antonio1000homens/led/hardware/enclosure/parts/01_panel_hinge_template_PRINT_1.scad

hinge_part = "panel_template";
include <../direct_mount_enclosure.scad>;
