antonio1000homens/led/hardware/enclosure/parts/02_hinged_equipment_base_PRINT_1.scad

hinge_part = "equipment_base";
include <../direct_mount_enclosure.scad>;
