antonio1000homens/led/hardware/enclosure/parts/03_universal_equipment_backplane_PRINT_1.scad

hinge_part = "universal_backplane";
include <../direct_mount_enclosure.scad>;
