antonio1000homens/led/hardware/enclosure/parts/04_left_equipment_side_PRINT_1.scad

hinge_part = "side_left";
include <../direct_mount_enclosure.scad>;
