antonio1000homens/led/hardware/enclosure/parts/05_right_equipment_side_PRINT_1.scad

hinge_part = "side_right";
include <../direct_mount_enclosure.scad>;
