antonio1000homens/led/hardware/enclosure/parts/08_matrixportal_s3_dock_PRINT_1.scad

include <../matrixportal/matrixportal_s3_mount.scad>;

// Fixed side-carried dock. The two keyed tabs snap into the MatrixPortal CAD
// left / front-view-right side. The rear face is solid and runs clear of the
// backplane boss tips so the complete side/dock/controller can withdraw
// together. The carrier still slides in separately on its dovetails.
matrixportal_s3_dock_print();
