antonio1000homens/led/hardware/enclosure/parts/10_matrixportal_s3_carrier_PRINT_1.scad

include <../matrixportal/matrixportal_s3_mount.scad>;

// Removable raised carrier. The PCB remains attached to this part and the
// complete assembly slides into the fixed dock from the left service opening.
matrixportal_s3_carrier_print();
