antonio1000homens/led/hardware/enclosure/parts/10_panel_pair_joiner_PRINT_3.scad

include <../panel_pair_joiner.scad>;
panel_pair_joiners_print(3);
