antonio1000homens/led/hardware/enclosure/parts/11_matrixportal_s3_keeper_PRINT_1.scad

include <../matrixportal/matrixportal_s3_mount.scad>;

// Print two copies. Each bar locks one column of the MatrixPortal's two
// mounting holes onto the carrier's fixed printed locating pins.
matrixportal_s3_keeper_print();
