antonio1000homens/led/hardware/enclosure/powersupply/02_service_tray_snap_dock_PRINT_1.scad

// Printable fixed dock for issue #177 PSU service tray.
include <service_tray_snap_latch_common.scad>;
snap_dock();
