antonio1000homens/led/hardware/enclosure/powersupply/03_service_tray_snap_tray_PRINT_1.scad

// Printable removable tray with integral pull-release flexure for issue #177.
include <service_tray_snap_latch_common.scad>;

// Stand the plate on its long lower edge. This puts the flexure anchor at the
// first layers so the 30 mm cantilever builds upward. The H2D process profile
// must enable support for the flexure. Z=0 is the tray's Y=+39.5 edge.
translate([0,0,tray_h/2])
    rotate([-90,0,0])
        snap_tray_with_detent();
