antonio1000homens/led/hardware/enclosure/schematics/00_complete_enclosure_CLOSED_ASSEMBLY.scad

// Complete four-module LED enclosure in the fully closed position.
// Assembly/reference view only; not a printable part.

include <../direct_mount_enclosure.scad>;

complete_direct_mount_assembly(0);
