antonio1000homens/led/hardware/enclosure/schematics/00_hinged_enclosure_ASSEMBLY.scad

hinge_part = "assembly";
include <../direct_mount_enclosure.scad>;
