antonio1000homens/led/hardware/enclosure/schematics/00_hinged_enclosure_CLOSED_ASSEMBLY.scad

include <../direct_mount_enclosure.scad>;
direct_mount_assembly(0);
