antonio1000homens/led/hardware/enclosure/schematics/matrixportal_s3_REFERENCE.scad

include <../matrixportal/matrixportal_s3_mount.scad>;

// Official Eagle-derived mechanical reference. This is not a printable part.
matrixportal_s3_reference(true);
