antonio1000homens/led/hardware/enclosure/direct-mount/parts/01_backplane_module_PRINT_3.scad

part = "backplane";
include <../direct_mount_enclosure.scad>;
