antonio1000homens/led/hardware/enclosure/direct-mount/parts/02_module_joiner_PRINT_4.scad

part = "joiner";
include <../direct_mount_enclosure.scad>;
