antonio1000homens/led/hardware/enclosure/direct-mount/parts/03_rod_end_plug_PRINT_4.scad

part = "rod_plug";
include <../direct_mount_enclosure.scad>;
