antonio1000homens/led/hardware/enclosure/direct-mount/parts/04_matrixportal_mount_PRINT_1.scad

part = "matrixportal_mount";
include <../direct_mount_enclosure.scad>;
