antonio1000homens/led/hardware/enclosure/direct-mount/parts/06_cable_clip_PRINT_8.scad

part = "cable_clip";
include <../direct_mount_enclosure.scad>;
