antonio1000homens/led/hardware/enclosure/direct-mount/parts/07_mounting_slot_coupon_PRINT_1.scad

part = "slot_coupon";
include <../direct_mount_enclosure.scad>;
