antonio1000homens/led/hardware/enclosure/direct-mount/parts/08_mount_pattern_template_PRINT_1.scad

part = "mount_pattern_template";
include <../direct_mount_enclosure.scad>;
