antonio1000homens/led/hardware/enclosure/direct-mount/docs/MECHANICAL_VALIDATION.md

# Hinged enclosure mechanical validation

The modular hinged design is the only supported direct-mount enclosure.

The canonical hinge motion follows PR #119: the equipment-side enclosure/base
remains stationary and the LED panel/template is the moving leaf.

## Automated gates

Run:

```bash
python hardware/enclosure/direct-mount/scripts/validate_enclosure.py
```

The validator regenerates all five canonical OpenSCAD parts and verifies:

- non-empty positive-volume meshes;
- watertight/single-shell geometry after mesh processing;
- bounded printable extents;
- a 2 mm voxel floating-layer/island proxy;
- no volumetric interference between the stationary base and removable backplane;
- positive backplane seating in the recessed rear base groove;
- top-down insertion clearance and 0.4 mm nominal groove clearance;
- dual **30 mm × 5 mm** structural side guides with 0.4 mm running clearance;
- the lower 30 mm stepped/narrowed backplane section and full-width shoulder above it;
- hidden guide-tower junctions kept within the bed-connected lower band;
- blind inside accessory bosses with a solid external rear skin;
- the 2 mm seat depth and rear-edge groove location;
- the 40 mm lower cavity, 60 mm taper start and 10 mm top depth;
- upper-only ventilation and the supported top closure;
- side-piece fit and hinge-rod clearance;
- an unobstructed lower equipment volume ahead of the rear groove;
- the stationary enclosure and 6 mm rail against the moving panel/template at
  **0, 15, 30, 45, 60, 75 and 90°**;
- neighboring module cores at the 256 mm pitch, with side retainers only at
  the outside edges;
- successful open and closed assembly-preview rendering.

The hinge regression contract includes:

- **14 mm** barrel OD;
- **7.2 mm** printed bore for the 6 mm rail;
- hinge axis at **y=27 mm, z=16 mm**;
- **7 mm** closed template-to-barrel clearance;
- local roots on the moving template only;
- rearward support webs that terminate at the reinforced hinge shelf;
- 3 mm local pads at the stationary hinge roots;
- **2 mm** stationary lower guard with **0.8 mm** barrel clearance.

The previous full-width captive tongue/channel is retired. The backplane enters
a 2 mm-deep **recessed groove at the rear of the base**. Its lower section is
vertical at the 40 mm equipment depth up to 60 mm; the upper enclosure then
tapers to 10 mm, carries ventilation slots, and grows a supported top closure
toward the moving template. The validator checks the rear-groove contract,
several positions along the vertical insertion path, the lower usable cavity,
and the complete hinge sweep.

The final automated manufacturing gate is Windsor Slicer/Bambu Studio using the
models in `.windsor-slicer.yaml`.

## Physical gates

Automated geometry cannot prove real FDM tolerances. Before printing four full
sets:

1. print one moving panel/template leaf and verify the six physical panel bosses;
2. print one stationary equipment base and verify the real 6 mm rail;
3. rotate the panel/template through the full **0–90°** arc while the equipment base remains fixed;
4. confirm the moving panel never contacts the stationary barrel support webs or lower guard;
5. print one universal backplane and confirm the narrowed lower 30 mm slides between both 5 mm guides, seats 2 mm into the rear groove, and removes upward;
6. confirm the guide towers retain the backplane laterally and the full-width shoulder clears their tops;
7. confirm the vertical lower wall, ventilated taper and top closure print without distortion;
8. verify the hidden guide-tower junctions and both outer side pieces engage while all exterior faces remain solid;
9. mate two equipment cores side-by-side at the 256 mm pitch and check the hidden pin/socket alignment;
10. test representative M3 hardware on the inward-facing lower boss grid and verify the external rear skin is unbroken;
11. verify connected HUB75/power cabling remains free through the opening arc.

Record tolerance changes in `direct_mount_enclosure.scad`; never patch an STL directly.
