antonio1000homens/led/hardware/matrixportal/firmware/display.py

"""Display backends: MatrixPortal S3 hardware and Wokwi visual fixture."""

import time

import board

from matrix_config import (
    MATRIX_ANIMATION_PROFILE,
    MATRIX_ANIMATION_PROFILES,
    MATRIX_BIT_DEPTH,
    MATRIX_EXPERIMENT_PRESET,
    CALLING_SCROLL_SPEED_OVERRIDE,
    MATRIX_PRESENTATION_MODE,
    MATRIX_RAIL_ROWS_SCROLL,
    MATRIX_REFRESH_FPS,
    MATRIX_STATS_INTERVAL_SECONDS,
    TODOIST_MARQUEE_PAUSE_SECONDS,
    TODOIST_MARQUEE_SPEED,
)

from brightness import BrightnessState, pixel_is_blocked

from formatting import (
    AGENDA_SLIDE_SECONDS,
    AGENDA_TITLE_X,
    AGENDA_VISIBLE_ROWS,
    QUEUE_VISIBLE_ROWS,
    agenda_scroll_state,
    agenda_marquee_x,
    agenda_title_marquee_x,
    calendar_due_text,
    todoist_due_label,
    calendar_row_parts,
    calendar_row_text,
    CALLING_LABEL,
    RAIL_MARQUEE_DELAY_SECONDS,
    CALLING_MARQUEE_PAUSE_SECONDS,
    calling_marquee_x,
    calling_color_segments,
    calling_text,
    rail_calling_timing,
    departure_scroll_state,
    DEPARTURE_SLIDE_SECONDS,
    DEPARTURE_RESET_GAP_SECONDS,
    DEPARTURE_RESET_SLIDE_SECONDS,
    RAIL_ROW_Y,
    RAIL_CALLING_SECONDS,
    RAIL_SUMMARY_SECONDS,
    rail_marquee_elapsed,
    rail_phase,
    rail_rows,
    ordinal_label,
    format_row,
    queue_scroll_state,
    row_slide_phase,
    service_status_text,
)


DISPLAY_WIDTH = 256
REMINDER_CLOCK_SIZE = 29
REMINDER_TEXT_X = 37
REMINDER_TEXT_SCALE = 3
REMINDER_SCROLL_SPEED = 64.0
REMINDER_SCROLL_GAP = 24


def reminder_scroll_x(screen, phase):
    """Continuously move the clock/text train from right to left and wrap it."""
    label = str(screen.get("label") or "")
    width = REMINDER_TEXT_X + len(label) * WEATHER_FONT_WIDTH * REMINDER_TEXT_SCALE
    travel = DISPLAY_WIDTH + width + REMINDER_SCROLL_GAP
    try:
        elapsed = max(0.0, float(phase or 0))
    except (TypeError, ValueError):
        elapsed = 0.0
    distance = int(elapsed * REMINDER_SCROLL_SPEED) % max(1, travel)
    return DISPLAY_WIDTH - distance


def reminder_clock_pixel(x, y):
    dx, dy = x - 14, y - 14
    return (156 <= dx * dx + dy * dy <= 205
            or (13 <= x <= 15 and 5 <= y <= 15)
            or (14 <= x <= 22 and 13 <= y <= 15))


STEAM_TRAIN_WIDTH = 52
STEAM_TRAIN_HEIGHT = 26
STEAM_TRAIN_VERTICAL_OFFSET = 1
STEAM_TRAIN_TEXT_GAP = 8
CLOCK_X = 226
HEADER_SLOT_X = 224
STALE_X = 190
QUEUE_FIRST_Y = 11
QUEUE_ROW_HEIGHT = 8
# The font label coordinate is a baseline. Start the three agenda rows lower
# so the final row uses the bottom of the 32px panel instead of leaving a
# visible unused band below it.
AGENDA_FIRST_Y = 11
AGENDA_ROW_HEIGHT = 8
WEATHER_ICON_WIDTH = 7
WEEKLY_WEATHER_ICON_SCALE = 2
TODAY_WEATHER_ICON_SCALE = 2
SUN_WEATHER_ICON_SCALE = 3
SUN_WEATHER_MOON_ICON_SCALE = 2
SUN_WEATHER_TIME_SCALE = 2
SUN_WEATHER_SUN_COLOR = 0xFFFF00
SUN_WEATHER_MOON_COLOR = 0x0000FF
SUN_WEATHER_ICON_Y = 5
SUN_WEATHER_ANIMATION_SECONDS = 4.0
SUN_WEATHER_COLOR_SECONDS = 4.0
SUN_WEATHER_TOTAL_ANIMATION_SECONDS = SUN_WEATHER_ANIMATION_SECONDS * 2
SUN_WEATHER_RISE_START_Y = 32
SUN_WEATHER_SET_START_Y = -(WEATHER_ICON_WIDTH * SUN_WEATHER_MOON_ICON_SCALE)
# MatrixDisplay labels use font baselines, while the fixture renderer uses
# top-left pixel coordinates. Keep fullscreen weather headers clear of the
# panel edge and align the forecast rows below them.
WEATHER_HEADING_BASELINE_Y = 9
WEATHER_HEADING_PIXEL_Y = 2
WEEKLY_WEATHER_ICON_Y = 10
WEEKLY_WEATHER_TEMPERATURE_Y = 25
TODAY_WEATHER_ICON_Y = 11
TODAY_WEATHER_TEMPERATURE_Y = 27
WEATHER_FULLSCREEN_KINDS = ("weather_weekly", "weather_today", "weather_sun")
NOVELTY_HEADING_Y = 5
NOVELTY_FIRST_LINE_Y = 14


def _novelty_page(screen, phase):
    """Wrap novelty text, advancing longer facts across pages during their slot."""
    message = str(screen.get("joke") if screen.get("kind") == "dad_joke" else screen.get("fact") or "")
    lines, current = [], ""
    for word in message.split():
        # Split unusually long uninterrupted words rather than silently clipping.
        while len(word) > 42:
            if current:
                lines.append(current)
                current = ""
            lines.append(word[:42])
            word = word[42:]
        if not word:
            continue
        candidate = (current + " " + word).strip()
        if len(candidate) > 42 and current:
            lines.append(current)
            current = word
        else:
            current = candidate
    if current:
        lines.append(current)
    if not lines:
        return []
    pages = (len(lines) + 2) // 3
    duration = max(1.0, float(screen.get("duration_seconds") or 15))
    page = min(pages - 1, int(max(0.0, float(phase)) * pages / duration))
    return lines[page * 3:page * 3 + 3]

WEEKLY_WEATHER_TEXT_SCALE = 1
WEEKLY_WEATHER_GLYPH_WIDTH = 3
WEEKLY_WEATHER_GLYPHS = {
    "0": (7, 5, 5, 5, 7), "1": (2, 6, 2, 2, 7),
    "2": (7, 1, 7, 4, 7), "3": (7, 1, 7, 1, 7),
    "4": (5, 5, 7, 1, 1), "5": (7, 4, 7, 1, 7),
    "6": (7, 4, 7, 5, 7), "7": (7, 1, 2, 2, 2),
    "8": (7, 5, 7, 5, 7), "9": (7, 5, 7, 1, 7),
    "S": (7, 4, 7, 1, 7), "U": (5, 5, 5, 5, 7),
    "N": (5, 7, 7, 7, 5), "R": (6, 5, 6, 5, 5),
    "I": (7, 2, 2, 2, 7), "E": (7, 4, 6, 4, 7),
    "T": (7, 2, 2, 2, 2), ":": (0, 4, 0, 4, 0),
    "C": (3, 4, 4, 4, 3), "-": (0, 0, 7, 0, 0),
}
WEATHER_FONT_WIDTH = 5
WEATHER_GAP = 1
HEADER_GAP = 4
HEADER_HOLD_SECONDS = 7.0
HEADER_SLOT_WIDTH = DISPLAY_WIDTH - HEADER_SLOT_X
CALLING_SCROLL_SPEED = 20.0
CALLING_SCROLL_GAP = 28
MIN_CALLING_SCROLL_SPEED = 10.0
MAX_CALLING_SCROLL_SPEED = 80.0
MIN_CALLING_SCROLL_GAP = 8
MAX_CALLING_SCROLL_GAP = 80
BIN_LORRY_SECONDS = 4.0
BIN_LORRY_SPEED = 64.0
BIN_LORRY_WIDTH = 52
BIN_LORRY_HEIGHT = 20
BIN_ICON_WIDTH = 9
BIN_ICON_HEIGHT = 12
BIN_ICON_Y = 10
BIN_TEXT_X = 40
BIN_TEXT_RIGHT = 220
BIN_COLORS = {
    "blue": 0x2255FF,
    "green": 0x22AA44,
    "black": 0x777777,
}
RAIL_ORDINAL_X = 0
RAIL_TIME_X = 24
RAIL_DESTINATION_X = 60
RAIL_PLATFORM_X = 152
RAIL_PLATFORM_WIDTH = 3 * WEATHER_FONT_WIDTH

WEATHER_ICONS = {
    # A compact round sun: the filled centre reads as a disc while the
    # separated cardinal and diagonal pixels remain visible at LED scale.
    "clear_day": (".......", "..###..", ".#####.", ".#####.", ".#####.", "..###..", "......."),
    "clear_night": ("...###.", "..###..", ".###...", ".###...", ".####..", "..####.", "...###."),
    "partly_cloudy_day": (".#.#...", "..#....", ".###...", "...##..", "..#####", ".######", "......."),
    "partly_cloudy_night": ("..##...", ".##....", ".###...", "...##..", "..#####", ".######", "......."),
    "cloudy": (".......", "...##..", "..####.", ".######", "#######", ".......", "......."),
    "fog": (".......", ".#####.", ".......", "#######", ".......", ".#####.", "......."),
    "rain": ("...##..", "..####.", ".######", "#######", "..#.#..", ".#.#...", "#.#...."),
    "snow": ("...##..", "..####.", ".######", "#######", ".#.#.#.", "..#.#..", ".#.#.#."),
    "storm": ("...##..", "..####.", ".######", "#######", "...##..", "..##...", "...#..."),
    "unknown": (".#####.", "##...##", "....##.", "...##..", "..##...", ".......", "..##..."),
}

WEATHER_COLORS = {
    "clear_day": 0xFFAA00,
    "clear_night": 0xAACCFF,
    "partly_cloudy_day": 0xFFCC55,
    "partly_cloudy_night": 0xAACCFF,
    "cloudy": 0xBBBBBB,
    "fog": 0x888888,
    "rain": 0x55AAFF,
    "snow": 0xFFFFFF,
    "storm": 0xFFCC00,
    "unknown": 0x888888,
}


def _clip(value, width):
    return str(value or "")[:max(0, int(width or 0))]


def _queue_parts(ride):
    state = "{}m".format(ride.get("wait_minutes", 0)) if ride.get("open") else "CLOSED"
    return str(ride.get("name") or "Unknown"), state


def _queue_row(ride):
    name, state = _queue_parts(ride)
    name = _clip(name, 24)
    name = name + (" " * max(0, 24 - len(name)))
    state = (" " * max(0, 8 - len(state))) + state
    return (name + state)[-32:]


def _weather_text(weather):
    if not isinstance(weather, dict):
        return None
    value = weather.get("temperature_c")
    if value is None:
        return "--C"
    try:
        return "{}C".format(int(round(float(value))))
    except (TypeError, ValueError):
        return "--C"


def _weather_icon(weather):
    if not isinstance(weather, dict):
        return None, WEATHER_ICONS["unknown"]
    name = str(weather.get("icon") or "unknown")
    return name, WEATHER_ICONS.get(name, WEATHER_ICONS["unknown"])


def _weather_rgb(icon_name, stale=False):
    color = WEATHER_COLORS.get(icon_name, WEATHER_COLORS["unknown"])
    return 0x777777 if stale else color


def _rail_weather_key(weather):
    """Return only weather fields that affect visible rail pixels."""
    if not isinstance(weather, dict):
        return None
    icon_name, _ = _weather_icon(weather)
    return (_weather_text(weather), icon_name, bool(weather.get("stale")))


def _next_periodic_boundary(elapsed, boundaries, cycle):
    """Seconds to the next state edge in a repeating animation cycle."""
    cycle = max(0.001, float(cycle))
    within = max(0.0, float(elapsed or 0)) % cycle
    candidates = []
    for boundary in boundaries:
        edge = float(boundary) % cycle
        delta = edge - within
        if delta <= 1e-6:
            delta += cycle
        candidates.append(delta)
    return min(candidates) if candidates else cycle


def _header_content_right(screen):
    return max(0, (STALE_X if screen.get("stale") else HEADER_SLOT_X) - HEADER_GAP)


def _right_aligned_x(text, right_edge):
    return max(0, int(right_edge) - len(str(text or "")) * WEATHER_FONT_WIDTH)


def _left_text(text, right_edge):
    return _clip(text, max(0, int(right_edge) // WEATHER_FONT_WIDTH))


def _fit_text_pixels(text, width):
    return _clip(text, max(0, int(width) // WEATHER_FONT_WIDTH))


def _weather_column_bounds(index, display_width=DISPLAY_WIDTH):
    """Return integer seven-column bounds without accumulating rounding error."""
    left = (int(index) * int(display_width)) // 7
    right = ((int(index) + 1) * int(display_width)) // 7
    return left, right


def _weekly_temperature_text(value):
    try:
        rounded = int(round(float(value)))
    except (TypeError, ValueError):
        return "--C"
    return "{}C".format(rounded)


def _weekly_weather_layout(days, display_width=DISPLAY_WIDTH):
    """Build renderer-neutral positions for up to seven forecast days."""
    if not isinstance(days, (list, tuple)):
        return []
    layout = []
    for index, raw_day in enumerate(days[:7]):
        day = raw_day if isinstance(raw_day, dict) else {}
        left, right = _weather_column_bounds(index, display_width)
        width = right - left
        weekday = _fit_text_pixels(str(day.get("weekday") or "").upper()[:3], width)
        maximum = _weekly_temperature_text(day.get("temperature_max_c"))
        icon_width = WEATHER_ICON_WIDTH * WEEKLY_WEATHER_ICON_SCALE
        maximum_width = len(maximum) * (WEEKLY_WEATHER_GLYPH_WIDTH + 1) * WEEKLY_WEATHER_TEXT_SCALE
        icon_name, rows = _weather_icon(day)

        def centered_x(text, pixel_width):
            return left + max(0, (width - pixel_width) // 2)

        layout.append({
            "index": index,
            "left": left,
            "right": right,
            "weekday": weekday,
            "weekday_x": centered_x(weekday, len(weekday) * WEATHER_FONT_WIDTH),
            "icon_name": icon_name,
            "icon_rows": rows,
            "icon_x": centered_x("", icon_width),
            "max_text": maximum,
            "max_x": left + max(0, (width - maximum_width) // 2),
            "icon_width": icon_width,
        })
    return layout


def _sun_weather_progress(phase):
    """Return the bounded entry-animation progress for the solar icons."""
    try:
        elapsed = max(0.0, float(phase or 0))
    except (TypeError, ValueError):
        elapsed = 0.0
    return min(1.0, elapsed / SUN_WEATHER_ANIMATION_SECONDS)


def _sun_weather_animation_active(phase):
    try:
        elapsed = max(0.0, float(phase or 0))
    except (TypeError, ValueError):
        elapsed = 0.0
    return elapsed < SUN_WEATHER_TOTAL_ANIMATION_SECONDS


def _sun_weather_local_phase(icon_name, phase):
    """Return the phase for one solar event in the sequential animation."""
    try:
        elapsed = max(0.0, float(phase or 0))
    except (TypeError, ValueError):
        elapsed = 0.0
    if icon_name == "clear_night":
        elapsed -= SUN_WEATHER_ANIMATION_SECONDS
    return min(SUN_WEATHER_ANIMATION_SECONDS, max(0.0, elapsed))


def _bin_collection_motion_state(screen, phase):
    """Return whether the bin lorry or collection label is moving."""
    try:
        elapsed = max(0.0, float(phase or 0))
    except (TypeError, ValueError):
        elapsed = 0.0
    if elapsed < BIN_LORRY_SECONDS:
        return True, max(0.05, BIN_LORRY_SECONDS - elapsed)
    labels = " / ".join(str(item.get("label") or "") for item in screen.get("collections") or [])
    label_width = len(labels) * 6
    if label_width <= BIN_TEXT_RIGHT - BIN_TEXT_X:
        return False, None
    try:
        speed = max(0.1, float(screen.get("slide_speed") or 20))
        elapsed = max(0.0, float(phase or 0))
    except (TypeError, ValueError):
        speed, elapsed = 20.0, 0.0
    cycle_distance = label_width + 24
    distance = (max(0.0, elapsed - BIN_LORRY_SECONDS) * speed) % cycle_distance
    if distance < label_width:
        return True, None
    return False, max(0.05, (cycle_distance - distance) / speed)


def _bin_collection_types(screen):
    """Map Home Assistant collection IDs to the bins shown on the board."""
    items = screen.get("collections") or []
    ids = " ".join(str(item.get("id") or "").lower() for item in items)
    labels = " ".join(str(item.get("label") or "").lower() for item in items)
    if "paper" in ids or "paper" in labels:
        return ("blue", "green", "black")
    if any(token in ids or token in labels for token in ("plastic", "plastics", "recycle-mixed")):
        return ("green",)
    return ("green",)


def _date_ordinal(value):
    """Convert a strict YYYY-MM-DD date to a Gregorian day number."""
    if not isinstance(value, str) or len(value) != 10 or value[4] != "-" or value[7] != "-":
        return None
    if not (value[:4].isdigit() and value[5:7].isdigit() and value[8:10].isdigit()):
        return None
    try:
        year, month, day = int(value[:4]), int(value[5:7]), int(value[8:10])
    except ValueError:
        return None
    if year < 1 or not 1 <= month <= 12:
        return None
    leap = year % 4 == 0 and (year % 100 != 0 or year % 400 == 0)
    month_lengths = (31, 29 if leap else 28, 31, 30, 31, 30, 31, 31, 30, 31, 30, 31)
    if not 1 <= day <= month_lengths[month - 1]:
        return None
    previous_year = year - 1
    days = previous_year * 365 + previous_year // 4 - previous_year // 100 + previous_year // 400
    days += sum(month_lengths[:month - 1]) + day - 1
    return days


def _bin_collection_due_label(collection_date, today):
    due_day = _date_ordinal(collection_date)
    today_day = _date_ordinal(today)
    if due_day is None or today_day is None:
        return "DUE DATE UNKNOWN"
    days_until = due_day - today_day
    if days_until < 0:
        return "OVERDUE"
    if days_until == 0:
        return "DUE TODAY"
    if days_until == 1:
        return "DUE IN 1 DAY"
    return "DUE IN {} DAYS".format(days_until)


def _bin_lorry_x(phase):
    """Slide a compact refuse lorry across the board from right to left."""
    try:
        elapsed = max(0.0, float(phase or 0))
    except (TypeError, ValueError):
        elapsed = 0.0
    return int(round(DISPLAY_WIDTH - elapsed * BIN_LORRY_SPEED))


def _format_sun_time(value):
    """Keep the time separator visible and normalize compact HHMM values."""
    text = str(value or "--:--")
    if len(text) == 4 and text.isdigit():
        return text[:2] + ":" + text[2:]
    return text


def _sun_weather_icon_y(icon_name, phase):
    """Slide sunrise upward and sunset downward to their shared resting row."""
    progress = _sun_weather_progress(_sun_weather_local_phase(icon_name, phase))
    # Smoothstep eases the icons into their final row instead of moving at a
    # constant speed and stopping abruptly. The clamped endpoint remains on
    # the panel for the rest of this screen's duration.
    progress = progress * progress * (3.0 - 2.0 * progress)
    if icon_name == "clear_day":
        icon_scale = SUN_WEATHER_ICON_SCALE
        start_y = SUN_WEATHER_RISE_START_Y
    elif icon_name == "clear_night":
        icon_scale = SUN_WEATHER_MOON_ICON_SCALE
        start_y = SUN_WEATHER_SET_START_Y
    else:
        return SUN_WEATHER_ICON_Y
    icon_size = WEATHER_ICON_WIDTH * icon_scale
    tile_size = WEATHER_ICON_WIDTH * SUN_WEATHER_ICON_SCALE
    rest_y = SUN_WEATHER_ICON_Y + (tile_size - icon_size) // 2
    return int(round(start_y + (rest_y - start_y) * progress))


def _sun_weather_color_progress(phase):
    try:
        elapsed = max(0.0, float(phase or 0))
    except (TypeError, ValueError):
        elapsed = 0.0
    progress = min(1.0, elapsed / SUN_WEATHER_COLOR_SECONDS)
    return progress * progress * (3.0 - 2.0 * progress)


def _sun_weather_rise_label_color(index, phase, stale=False):
    if stale:
        return 0x777777
    progress = _sun_weather_color_progress(_sun_weather_local_phase("clear_day", phase))
    yellow_letters = min(7, int(progress * 8))
    return 0xFFFF00 if index < yellow_letters else 0x0000FF


def _sun_weather_set_label_color(index, phase, stale=False):
    progress = _sun_weather_color_progress(_sun_weather_local_phase("clear_night", phase))
    # Reveal one additional sunset letter at a time from yellow to blue.
    blue_letters = min(6, int(progress * 7))
    if index < blue_letters:
        return 0x777777 if stale else 0x0000FF
    return 0x777777 if stale else 0xFFAA00


def _sun_weather_rgb(icon_name, stale=False, phase=0):
    """Keep the sunrise sun yellow and the moon blue throughout the animation."""
    if stale:
        return 0x777777
    if icon_name == "clear_night":
        return SUN_WEATHER_MOON_COLOR
    return SUN_WEATHER_SUN_COLOR


def _today_weather_layout(blocks, display_width=DISPLAY_WIDTH):
    """Build six rolling four-hour Weather columns beginning with Now."""
    if not isinstance(blocks, (list, tuple)):
        return []
    layout = []
    for index, raw_block in enumerate(blocks[:6]):
        block = raw_block if isinstance(raw_block, dict) else {}
        left = (index * int(display_width)) // 6
        right = ((index + 1) * int(display_width)) // 6
        width = right - left
        label = str(block.get("label") or "")[:5]
        temperature = _weekly_temperature_text(block.get("temperature_c"))
        icon_name, rows = _weather_icon(block)
        icon_width = WEATHER_ICON_WIDTH * TODAY_WEATHER_ICON_SCALE
        temp_width = len(temperature) * (WEEKLY_WEATHER_GLYPH_WIDTH + 1)
        layout.append({
            "left": left,
            "right": right,
            "label": label,
            "label_x": left + max(0, (width - len(label) * WEATHER_FONT_WIDTH) // 2),
            "icon_name": icon_name,
            "icon_rows": rows,
            "icon_x": left + max(0, (width - icon_width) // 2),
            "icon_width": icon_width,
            "temp_text": temperature,
            "temp_x": left + max(0, (width - temp_width) // 2),
        })
    return layout


def _calling_segments(text, x, gap):
    """Return clipped station-label segments that cannot overwrite the prefix."""
    text = str(text or "")
    stations = text[len(CALLING_LABEL):] if text.startswith(CALLING_LABEL) else text
    station_width = len(stations) * WEATHER_FONT_WIDTH
    prefix_width = len(CALLING_LABEL) * WEATHER_FONT_WIDTH
    segments = []
    for candidate_x in (int(x), int(x) + station_width + int(gap)):
        if candidate_x >= DISPLAY_WIDTH or candidate_x + station_width <= prefix_width:
            continue
        drop = max(0, (prefix_width - candidate_x + WEATHER_FONT_WIDTH - 1) // WEATHER_FONT_WIDTH)
        visible_x = candidate_x + drop * WEATHER_FONT_WIDTH
        visible = stations[drop:]
        visible = visible[:max(0, (DISPLAY_WIDTH - visible_x) // WEATHER_FONT_WIDTH)]
        if visible:
            segments.append((visible_x, visible))
    return segments


def _bounded_number(value, default, minimum, maximum):
    try:
        number = float(value)
    except (TypeError, ValueError):
        number = float(default)
    return min(float(maximum), max(float(minimum), number))


def _station_scroll_settings(screen):
    if CALLING_SCROLL_SPEED_OVERRIDE is not None:
        try:
            # The board-local experiment intentionally sits outside the
            # admin-configured minimum, so do not clamp it back to 10 px/s.
            speed = max(1.0, float(CALLING_SCROLL_SPEED_OVERRIDE))
        except (TypeError, ValueError):
            speed = CALLING_SCROLL_SPEED
    else:
        speed = _bounded_number(
            screen.get("station_scroll_speed"),
            CALLING_SCROLL_SPEED,
            MIN_CALLING_SCROLL_SPEED,
            MAX_CALLING_SCROLL_SPEED,
        )
    gap = int(round(_bounded_number(
        screen.get("station_list_spacing"),
        CALLING_SCROLL_GAP,
        MIN_CALLING_SCROLL_GAP,
        MAX_CALLING_SCROLL_GAP,
    )))
    return speed, gap


def _weather_group_layout(weather, offset=0):
    text = _weather_text(weather) or "--C"
    width = WEATHER_ICON_WIDTH + WEATHER_GAP + len(text) * WEATHER_FONT_WIDTH
    group_x = max(0, DISPLAY_WIDTH - width) + int(offset)
    return text, group_x, group_x + WEATHER_ICON_WIDTH + WEATHER_GAP


def _header_item_state(phase, weather):
    """Return the stationary clock or weather item for the top-right slot."""
    if not isinstance(weather, dict):
        return "clock", 0
    try:
        phase = max(0.0, float(phase or 0))
    except (TypeError, ValueError):
        phase = 0.0
    within = phase % (HEADER_HOLD_SECONDS * 2)
    return ("clock", 0) if within < HEADER_HOLD_SECONDS else ("weather", 0)


def _header_slide_active(phase, weather):
    """The clock/weather slot switches at rest and has no moving interval."""
    return False


def _header_next_boundary_seconds(phase, weather):
    if not isinstance(weather, dict):
        return 60.0
    try:
        phase = max(0.0, float(phase or 0))
    except (TypeError, ValueError):
        phase = 0.0
    cycle = HEADER_HOLD_SECONDS * 2
    within = phase % cycle
    for boundary in (HEADER_HOLD_SECONDS, cycle):
        if boundary > within + 1e-9:
            return max(0.05, boundary - within)
    return max(0.05, cycle - within)


def _rail_columns(service, ordinal=1):
    return (
        ordinal_label(ordinal),
        _clip(service.get("time", "--:--"), 5),
        str(service.get("destination") or "Unknown"),
        ("P" + str(service.get("platform", "-")))[:3],
        service_status_text(service),
    )


def _rgb_tuple(color):
    return ((color >> 16) & 0xFF, (color >> 8) & 0xFF, color & 0xFF)


def _agenda_state(screen, phase):
    events = screen.get("events") or []
    visible = max(1, int(screen.get("viewport_size") or AGENDA_VISIBLE_ROWS))
    page_seconds = screen.get("page_seconds") or 5
    start, progress = agenda_scroll_state(phase, len(events), page_seconds, visible)
    return events, visible, start, progress


def _calendar_due_layout(screen, clock_date, clock_time):
    """Keep the legacy header countdown for non-Todoist calendar feeds."""
    if screen.get("kind") != "calendar_agenda" or screen.get("source") == "todoist":
        return "", 0
    events = screen.get("events") or []
    if not events:
        return "", 0
    text = calendar_due_text(events[0], clock_date, clock_time)
    if not text:
        return "", 0
    right_edge = (STALE_X if screen.get("stale") else HEADER_SLOT_X) - HEADER_GAP
    return text, max(0, right_edge - len(text) * WEATHER_FONT_WIDTH)


class MatrixDisplay:
    def __init__(self, brightness_percent=100):
        import displayio
        import framebufferio
        import rgbmatrix
        from adafruit_bitmap_font import bitmap_font
        from adafruit_display_text import label

        displayio.release_displays()
        matrix = rgbmatrix.RGBMatrix(
            width=DISPLAY_WIDTH,
            height=32,
            # Four chained 64x32 panels need refresh headroom. Two bits per
            # channel retain the board's text/status colours while matching
            # the MatrixPortal helper's flicker-resistant default.
            bit_depth=MATRIX_BIT_DEPTH,
            doublebuffer=True,
            addr_pins=board.MTX_ADDRESS[:4],
            **board.MTX_COMMON,
        )
        # Keep scene construction identical while issue #70 varies only the
        # framebuffer presentation strategy.
        if MATRIX_PRESENTATION_MODE not in ("target_fps", "immediate", "auto_refresh"):
            raise ValueError(
                "MATRIX_PRESENTATION_MODE must be target_fps, immediate, or auto_refresh"
            )
        self.presentation_mode = MATRIX_PRESENTATION_MODE
        self.display = framebufferio.FramebufferDisplay(
            matrix,
            auto_refresh=self.presentation_mode == "auto_refresh",
        )
        self.display.root_group = displayio.Group()
        self._refresh_misses = 0

        self._brightness = BrightnessState(brightness_percent)
        self._brightness_bitmap = displayio.Bitmap(DISPLAY_WIDTH, 32, 2)
        self._brightness_palette = displayio.Palette(2)
        self._brightness_palette[0] = 0x000000
        self._brightness_palette.make_transparent(0)
        self._brightness_palette[1] = 0x000000
        self._brightness_overlay = displayio.TileGrid(
            self._brightness_bitmap,
            pixel_shader=self._brightness_palette,
        )
        self._brightness_overlay_parent = None
        self._render_brightness_overlay()

        self.label_type = label.Label
        self.font = bitmap_font.load_font("/font5x7.pcf")

        # Low-overhead aggregate metrics for the physical-board comparison.
        now = time.monotonic()
        self._stats_started = now
        self._stats_last_report = now
        self._stats_heap_start = self._heap_free()
        self._stats_changes = 0
        self._stats_refresh_attempts = 0
        self._stats_refresh_successes = 0
        self._stats_refresh_failures = 0
        self._stats_last_success = None
        self._stats_interval_min = None
        self._stats_interval_max = None
        self._stats_interval_total = 0.0
        self._stats_interval_count = 0
        self._stats_animation_ticks = 0
        self._stats_todoist_ticks = 0
        self._stats_todoist_changed = 0
        self._stats_rail_ticks = 0
        self._stats_rail_changed = 0
        self._stats_update_total = 0.0
        self._stats_update_max = 0.0
        self._stats_refresh_total = 0.0
        self._stats_refresh_max = 0.0
        self._stats_rail_update_heap_gain_max = 0
        self._stats_rail_refresh_heap_gain_max = 0
        self._stats_fetch_overlap = 0
        self._stats_cadence_switches = 0
        self._stats_animation_classes = {
            name: {
                "ticks": 0,
                "changed": 0,
                "update_total": 0.0,
                "update_max": 0.0,
                "refresh_total": 0.0,
                "refresh_max": 0.0,
            }
            for name in (
                "todoist_marquee",
                "todoist_page_slide",
                "header_slide",
                "departures_calling",
                "weather_sun_slide",
            )
        }
        print(
            "MATRIX PRESENTATION preset={} animation_profile={} rail_rows_scroll={} mode={} target_fps={} marquee_px_s={} calling_px_s={} auto_refresh={}".format(
                MATRIX_EXPERIMENT_PRESET,
                MATRIX_ANIMATION_PROFILE,
                MATRIX_RAIL_ROWS_SCROLL,
                self.presentation_mode,
                MATRIX_REFRESH_FPS,
                TODOIST_MARQUEE_SPEED,
                CALLING_SCROLL_SPEED_OVERRIDE,
                self.display.auto_refresh,
            )
        )

        # Todoist is the only Matrix page that continuously animates while the
        # rest of the board is in static mode. Keep its display tree alive and
        # mutate group coordinates instead of rebuilding labels, bitmaps and
        # masks for every frame.
        self._todoist_group = None
        self._todoist_rows = []
        self._todoist_events = None
        self._todoist_clock_date = None
        self._todoist_title = None
        self._todoist_stale = None
        self._todoist_viewport_size = None
        self._todoist_page_step = 1
        self._todoist_page_seconds = None
        self._todoist_page_starts = ()
        self._todoist_page_durations = ()
        self._todoist_weather_icon = None
        self._todoist_weather_temp = None
        self._todoist_weather_stale = None
        self._todoist_clock_group = None
        self._todoist_clock_label = None
        self._todoist_weather_group = None

        # Departures use the same persistent-scene approach as Todoist.  Only
        # the calling-at labels move between frames; rebuilding the complete
        # four-panel scene is deliberately avoided.
        self._rail_scenes = {}
        self._rail_group = None
        self._rail_services = None
        self._rail_title = None
        self._rail_stale = None
        self._rail_weather = None
        self._rail_calling_labels = []
        self._rail_departure_rows = []
        self._rail_phase = None
        self._rail_clock_group = None
        self._rail_clock_label = None
        self._rail_weather_group = None

        # The departures intro is a full-screen persistent scene. The train,
        # wheels and trailing text are constructed once; animation only moves
        # the containing group horizontally.
        self._steam_train_group = None
        self._steam_train_motion_group = None
        self._steam_train_words = None
        self._steam_train_speed = None

        # The solar-times screen only animates its two icon TileGrids. Keep
        # the scene alive during the short entry transition so the physical
        # board does not rebuild the complete display tree every frame.
        self._sun_group = None
        self._sun_key = None
        self._sun_icon_grids = ()
        self._sun_label_grids = ()

        # MQTT collection labels can scroll for the full screen duration.
        # Keep their labels and header scene persistent across frames.
        self._bin_group = None
        self._bin_key = None
        self._bin_weather = None
        self._bin_header_kind = None
        self._bin_label = None
        self._bin_title = None
        self._bin_date_group = None
        self._bin_date = None
        self._bin_footer_group = None
        self._bin_stale = None
        self._bin_clock_label = None
        self._bin_header_group = None
        self._bin_content_group = None
        self._bin_bins_group = None
        self._bin_lorry_group = None
        self._bin_lorry_grid = None
        self._bin_lorry_label = None
        self._bin_types = ()

    @property
    def brightness_percent(self):
        return self._brightness.percent

    def _render_brightness_overlay(self):
        percent = self._brightness.percent
        if percent >= 100:
            self._brightness_bitmap.fill(0)
            return
        for y in range(32):
            for x in range(DISPLAY_WIDTH):
                self._brightness_bitmap[x, y] = 1 if pixel_is_blocked(x, y, percent) else 0

    def _attach_brightness_overlay(self, group, bring_to_front=False):
        parent = self._brightness_overlay_parent
        if parent is group:
            if bring_to_front:
                try:
                    group.remove(self._brightness_overlay)
                except ValueError:
                    pass
                group.append(self._brightness_overlay)
            return

        if parent is not None:
            try:
                parent.remove(self._brightness_overlay)
            except ValueError:
                pass
        group.append(self._brightness_overlay)
        self._brightness_overlay_parent = group

    def adjust_brightness(self, direction):
        """Adjust apparent brightness without changing HUB75 scan timing."""
        percent, changed = self._brightness.adjust(direction)
        if not changed:
            return percent
        self._render_brightness_overlay()
        if self._brightness_overlay_parent is not None:
            self._refresh()
        print("BRIGHTNESS {}%".format(percent))
        return percent

    def set_brightness_percent(self, percent):
        """Apply the persisted display brightness received from the screen API."""
        next_percent, changed = self._brightness.set(percent)
        if not changed:
            return next_percent
        self._render_brightness_overlay()
        if self._brightness_overlay_parent is not None:
            self._refresh()
        print("BRIGHTNESS {}% (admin)".format(next_percent))
        return next_percent

    def _label(self, group, text, color, x, y):
        item = self.label_type(self.font, text=str(text), color=color, x=int(x), y=int(y))
        group.append(item)
        return item

    def _temperature_label(self, group, text, color, x, y):
        import displayio

        scale = WEEKLY_WEATHER_TEXT_SCALE
        bitmap = displayio.Bitmap(len(text) * (WEEKLY_WEATHER_GLYPH_WIDTH + 1) * scale, 5 * scale, 2)
        palette = displayio.Palette(2)
        palette[0] = 0x000000
        palette.make_transparent(0)
        palette[1] = color
        for index, char in enumerate(str(text)):
            rows = WEEKLY_WEATHER_GLYPHS.get(char, (0, 0, 0, 0, 0))
            for row_index, row_bits in enumerate(rows):
                for column in range(WEEKLY_WEATHER_GLYPH_WIDTH):
                    if row_bits & (1 << (WEEKLY_WEATHER_GLYPH_WIDTH - column - 1)):
                        for dx in range(scale):
                            for dy in range(scale):
                                bitmap[index * (WEEKLY_WEATHER_GLYPH_WIDTH + 1) * scale + column * scale + dx,
                                       row_index * scale + dy] = 1
        group.append(displayio.TileGrid(bitmap, pixel_shader=palette, x=int(x), y=int(y)))

    def _scaled_label(self, group, text, color, x, y, scale=3):
        """Draw font glyphs into a scaled bitmap for the compact train intro."""
        import displayio

        if not hasattr(self.font, "get_glyph"):
            return self._label(group, text, color, x, y + 9)
        text = str(text)
        if hasattr(self.font, "load_glyphs"):
            self.font.load_glyphs(set(ord(character) for character in text))
        ascent = getattr(self.font, "ascent", None)
        if ascent is None:
            ascent = self.font.get_bounding_box()[1]
        y_offset = ascent // 2
        glyphs = []
        cursor_x = min_x = min_y = 0
        max_x = max_y = 0
        for character in text:
            glyph = self.font.get_glyph(ord(character))
            if glyph is None:
                continue
            glyph_x = cursor_x + glyph.dx
            glyph_y = -glyph.height - glyph.dy + y_offset
            glyphs.append((glyph, glyph_x, glyph_y))
            min_x = min(min_x, glyph_x)
            max_x = max(max_x, glyph_x + glyph.width)
            min_y = min(min_y, glyph_y)
            max_y = max(max_y, glyph_y + glyph.height)
            cursor_x += glyph.shift_x
        width = max(1, max(max_x, cursor_x) - min_x)
        height = max(1, max_y - min_y)
        bitmap = displayio.Bitmap(width * scale, height * scale, 2)
        palette = displayio.Palette(2)
        palette[0] = 0x000000
        palette.make_transparent(0)
        palette[1] = color
        for glyph, glyph_x, glyph_y in glyphs:
            for gy in range(glyph.height):
                for gx in range(glyph.width):
                    if glyph.bitmap[gx, gy]:
                        for dy in range(scale):
                            for dx in range(scale):
                                bitmap[(glyph_x - min_x + gx) * scale + dx,
                                       (glyph_y - min_y + gy) * scale + dy] = 1
        group.append(displayio.TileGrid(bitmap, pixel_shader=palette,
                                        x=int(x), y=int(y)))

    def _chunked_label_group(self, text, color, y, chunk_chars=24):
        """Build fixed text chunks so scrolling moves groups without reflowing labels."""
        import displayio

        group = displayio.Group()
        text = str(text or "")
        if not text:
            self._label(group, "", color, 0, y)
            return group
        for start in range(0, len(text), chunk_chars):
            self._label(
                group,
                text[start:start + chunk_chars],
                color,
                start * WEATHER_FONT_WIDTH,
                y,
            )
        return group

    def _calling_label_group(self, service, y, prepared_segments=None):
        import displayio

        group = displayio.Group()
        if prepared_segments:
            segments = [
                (
                    segment.get("text", ""),
                    0xFFFFFF if segment.get("role") == "station" else 0xFFAA00,
                )
                for segment in prepared_segments
                if isinstance(segment, dict)
            ]
        else:
            segments = calling_color_segments(service)
        if not segments:
            return group

        # Lightweight host fixtures use a label-only fake font. The real
        # MatrixPortal bitmap font exposes glyph metrics and takes the compact
        # single-bitmap path below.
        if not hasattr(self.font, "get_glyph"):
            cursor = 0
            for text, color in segments:
                self._label(group, text, color, cursor, y)
                cursor += len(text) * WEATHER_FONT_WIDTH
            return group

        characters = set()
        for text, _ in segments:
            for character in text:
                characters.add(ord(character))
        if hasattr(self.font, "load_glyphs"):
            self.font.load_glyphs(characters)

        ascent = getattr(self.font, "ascent", None)
        if ascent is None:
            ascent = self.font.get_bounding_box()[1]
        y_offset = ascent // 2
        glyphs = []
        cursor_x = 0
        min_x = 0
        max_x = 0
        min_y = 0
        max_y = 0
        for text, color in segments:
            color_index = 1 if color == 0xFFFFFF else 2
            for character in text:
                glyph = self.font.get_glyph(ord(character))
                if glyph is None:
                    continue
                glyph_x = cursor_x + glyph.dx
                glyph_y = -glyph.height - glyph.dy + y_offset
                glyphs.append((glyph, glyph_x, glyph_y, color_index))
                min_x = min(min_x, glyph_x)
                max_x = max(max_x, glyph_x + glyph.width)
                min_y = min(min_y, glyph_y)
                max_y = max(max_y, glyph_y + glyph.height)
                cursor_x += glyph.shift_x

        width = max(1, max(max_x, cursor_x) - min_x)
        height = max(1, max_y - min_y)
        bitmap = displayio.Bitmap(width, height, 3)
        palette = displayio.Palette(3)
        palette[0] = 0x000000
        palette.make_transparent(0)
        palette[1] = 0xFFFFFF
        palette[2] = 0xFFAA00
        for glyph, glyph_x, glyph_y, color_index in glyphs:
            for glyph_y_offset in range(glyph.height):
                for glyph_x_offset in range(glyph.width):
                    if glyph.bitmap[glyph_x_offset, glyph_y_offset]:
                        bitmap[
                            glyph_x + glyph_x_offset - min_x,
                            glyph_y + glyph_y_offset - min_y,
                        ] = color_index

        group.append(
            displayio.TileGrid(
                bitmap,
                pixel_shader=palette,
                x=min_x,
                y=y + min_y,
            )
        )
        return group

    def _mask(self, group, x, y, width, height=8):
        import displayio

        width = max(1, int(width))
        height = max(1, int(height))
        bitmap = displayio.Bitmap(width, height, 2)
        palette = displayio.Palette(2)
        palette[0] = 0x000000
        palette[1] = 0x000000
        group.append(displayio.TileGrid(bitmap, pixel_shader=palette, x=int(x), y=int(y)))

    def _header_mask(self, group):
        self._mask(group, 0, 0, DISPLAY_WIDTH, 8)

    def _heap_free(self):
        try:
            import gc
            return gc.mem_free() if hasattr(gc, "mem_free") else None
        except (ImportError, AttributeError):
            return None

    def _record_success_interval(self, now):
        if self._stats_last_success is not None:
            interval = max(0.0, now - self._stats_last_success)
            if self._stats_interval_min is None or interval < self._stats_interval_min:
                self._stats_interval_min = interval
            if self._stats_interval_max is None or interval > self._stats_interval_max:
                self._stats_interval_max = interval
            self._stats_interval_total += interval
            self._stats_interval_count += 1
        self._stats_last_success = now

    def _maybe_report_stats(self):
        now = time.monotonic()
        if now - self._stats_last_report < MATRIX_STATS_INTERVAL_SECONDS:
            return
        elapsed = max(0.001, now - self._stats_started)
        if self.presentation_mode == "auto_refresh":
            presented_fps = "n/a"
        else:
            presented_fps = "{:.2f}".format(self._stats_refresh_successes / elapsed)
        interval_avg = (
            self._stats_interval_total / self._stats_interval_count
            if self._stats_interval_count
            else None
        )
        print(
            "MATRIX STATS mode={} target_fps={} elapsed={:.1f} changes={} "
            "refresh_attempts={} refresh_successes={} refresh_failures={} "
            "presented_fps={} interval_min={} interval_max={} interval_avg={} "
            "heap_start={} heap_end={} animation_ticks={} todoist_ticks={} "
            "todoist_changed={} rail_ticks={} rail_changed={} "
            "update_avg={} update_max={} refresh_avg={} refresh_max={} "
            "fetch_overlap={} cadence_switches={} "
            "todoist_marquee_ticks={} todoist_marquee_changed={} "
                "todoist_page_slide_ticks={} todoist_page_slide_changed={} "
                "todoist_marquee_update_max={} todoist_marquee_refresh_max={} "
                "todoist_page_update_max={} todoist_page_refresh_max={} "
                "header_slide_ticks={} header_slide_changed={} "
                "header_slide_update_max={} header_slide_refresh_max={} "
                "departures_calling_ticks={} departures_calling_changed={} "
                "departures_calling_update_max={} departures_calling_refresh_max={} "
                "departures_update_heap_gain={} departures_refresh_heap_gain={}".format(
                self.presentation_mode,
                MATRIX_REFRESH_FPS,
                elapsed,
                self._stats_changes,
                self._stats_refresh_attempts,
                self._stats_refresh_successes,
                self._stats_refresh_failures,
                presented_fps,
                "{:.4f}".format(self._stats_interval_min)
                if self._stats_interval_min is not None
                else "n/a",
                "{:.4f}".format(self._stats_interval_max)
                if self._stats_interval_max is not None
                else "n/a",
                "{:.4f}".format(interval_avg) if interval_avg is not None else "n/a",
                self._stats_heap_start,
                self._heap_free(),
                self._stats_animation_ticks,
                self._stats_todoist_ticks,
                self._stats_todoist_changed,
                self._stats_rail_ticks,
                self._stats_rail_changed,
                "{:.4f}".format(self._stats_update_total / self._stats_animation_ticks)
                if self._stats_animation_ticks else "n/a",
                "{:.4f}".format(self._stats_update_max),
                "{:.4f}".format(self._stats_refresh_total / self._stats_refresh_successes)
                if self._stats_refresh_successes else "n/a",
                "{:.4f}".format(self._stats_refresh_max),
                self._stats_fetch_overlap,
                self._stats_cadence_switches,
                self._stats_animation_classes["todoist_marquee"]["ticks"],
                self._stats_animation_classes["todoist_marquee"]["changed"],
                self._stats_animation_classes["todoist_page_slide"]["ticks"],
                self._stats_animation_classes["todoist_page_slide"]["changed"],
                "{:.4f}".format(self._stats_animation_classes["todoist_marquee"]["update_max"]),
                "{:.4f}".format(self._stats_animation_classes["todoist_marquee"]["refresh_max"]),
                "{:.4f}".format(self._stats_animation_classes["todoist_page_slide"]["update_max"]),
                "{:.4f}".format(self._stats_animation_classes["todoist_page_slide"]["refresh_max"]),
                self._stats_animation_classes["header_slide"]["ticks"],
                self._stats_animation_classes["header_slide"]["changed"],
                "{:.4f}".format(self._stats_animation_classes["header_slide"]["update_max"]),
                "{:.4f}".format(self._stats_animation_classes["header_slide"]["refresh_max"]),
                self._stats_animation_classes["departures_calling"]["ticks"],
                self._stats_animation_classes["departures_calling"]["changed"],
                "{:.4f}".format(self._stats_animation_classes["departures_calling"]["update_max"]),
                "{:.4f}".format(self._stats_animation_classes["departures_calling"]["refresh_max"]),
                self._stats_rail_update_heap_gain_max,
                self._stats_rail_refresh_heap_gain_max,
            )
        )
        self._stats_last_report = now

    def note_fetch_overlap(self):
        """Record a blocking fetch that occurred while animation was active."""
        self._stats_fetch_overlap += 1

    def note_cadence_switch(self):
        self._stats_cadence_switches += 1

    def _animation_class(self, screen, phase):
        """Return the active animation class without changing its cadence."""
        if not isinstance(screen, dict):
            return None
        kind = screen.get("kind")
        if kind == "flash":
            return "queue_rows"
        if kind == "calendar_agenda" and screen.get("source") == "todoist":
            if self._todoist_rows and self._todoist_page_slide_active(phase):
                return "todoist_page_slide"
            if _header_slide_active(phase, screen.get("weather")):
                return "header_slide"
            if self._todoist_rows and self._todoist_titles_moving(phase):
                return "todoist_marquee"
            return None
        if kind == "steam_train_intro":
            return "queue_rows"
        if kind == "rail_combined":
            calling_seconds = screen.get("calling_seconds", RAIL_CALLING_SECONDS)
            summary_seconds = screen.get("summary_seconds", RAIL_SUMMARY_SECONDS)
            if _header_slide_active(phase, screen.get("weather")):
                return "header_slide"
            if self._departures_rows_moving(screen, phase, calling_seconds, summary_seconds):
                return "departures_calling"
            if self._departures_calling_moving(screen, phase, calling_seconds, summary_seconds):
                return "departures_calling"
        if kind == "theme_park_queues":
            parks = screen.get("parks") or (screen,)
            if screen.get("splash_enabled") or len(parks) > 1:
                return "queue_rows"
            for park in parks:
                if len(park.get("rides") or ()) > QUEUE_VISIBLE_ROWS:
                    return "queue_rows"
        if kind == "weather_sun" and _sun_weather_animation_active(phase):
            return "weather_sun_slide"
        if kind == "bin_collection":
            moving, _ = _bin_collection_motion_state(screen, phase)
            if moving:
                return "todoist_marquee"
            if _header_slide_active(phase, screen.get("weather")):
                return "header_slide"
        return None

    def animation_cadence(self, screen, phase):
        """Return the desired update cadence for the active partial scene."""
        if (
            isinstance(screen, dict)
            and screen.get("kind") == "bin_collection"
            and self._animation_class(screen, phase) is None
        ):
            return 0
        if MATRIX_ANIMATION_PROFILE == "baseline":
            return MATRIX_REFRESH_FPS
        animation_class = self._animation_class(screen, phase)
        if animation_class is None:
            return 0
        return MATRIX_ANIMATION_PROFILES[MATRIX_ANIMATION_PROFILE][animation_class]

    def animation_active(self, screen, phase):
        """Return whether the screen has pixels moving at this phase."""
        return self._animation_class(screen, phase) is not None

    def animation_sleep_seconds(self, screen, phase):
        """Return a conservative sleep until the next known animation boundary."""
        if not isinstance(screen, dict):
            return None
        kind = screen.get("kind")
        if kind == "bin_collection":
            moving, gap_remaining = _bin_collection_motion_state(screen, phase)
            if not moving and gap_remaining is not None:
                return gap_remaining
            if gap_remaining is None:
                return max(0.05, _header_next_boundary_seconds(phase, screen.get("weather")))
        if kind == "calendar_agenda" and screen.get("source") == "todoist":
            if self._todoist_rows:
                try:
                    phase = max(0.0, float(phase or 0))
                except (TypeError, ValueError):
                    phase = 0.0
                if self._todoist_page_slide_active(phase):
                    return 0.0
                visible = self._todoist_viewport_size
                longest_scroll = 0.0
                for row in self._todoist_rows[:visible]:
                    longest_scroll = max(
                        longest_scroll,
                        self._todoist_title_scroll_seconds(row[2], row[3]),
                    )
                transition_at = self._todoist_page_transition_at(0)
                boundaries = []
                if phase < longest_scroll:
                    boundaries.append(longest_scroll - phase)
                if phase < transition_at:
                    boundaries.append(transition_at - phase)
                boundaries.append(_header_next_boundary_seconds(phase, screen.get("weather")))
                return max(0.05, min(boundaries))
        if kind == "rail_combined":
            calling_seconds = screen.get("calling_seconds", RAIL_CALLING_SECONDS)
            summary_seconds = screen.get("summary_seconds", RAIL_SUMMARY_SECONDS)
            boundaries = [_header_next_boundary_seconds(phase, screen.get("weather"))]
            try:
                value = max(0.0, float(phase or 0))
            except (TypeError, ValueError):
                value = 0.0
            cycle = summary_seconds + calling_seconds
            within = value % cycle
            if rail_phase(phase, summary_seconds, calling_seconds) == "summary":
                boundaries.append(summary_seconds - within)
            else:
                boundaries.append(cycle - within)
                calling_elapsed = rail_marquee_elapsed(phase, summary_seconds, calling_seconds)
                services = screen.get("services") or ()
                upcoming_count = max(0, len(services) - 1)
                pause = max(0.0, float(screen.get("upcoming_train_pause_seconds", 2) or 0))
                max_start = max(0, upcoming_count - 2)
                if max_start and MATRIX_RAIL_ROWS_SCROLL:
                    step = pause + DEPARTURE_SLIDE_SECONDS
                    normal = (max_start + 1) * step
                    row_cycle = normal + DEPARTURE_RESET_GAP_SECONDS + DEPARTURE_RESET_SLIDE_SECONDS
                    row_edges = [0.0, normal, normal + DEPARTURE_RESET_GAP_SECONDS,
                                 row_cycle]
                    for index in range(max_start + 1):
                        start = index * step + pause
                        row_edges.extend((start, start + DEPARTURE_SLIDE_SECONDS))
                    boundaries.append(_next_periodic_boundary(calling_elapsed, row_edges, row_cycle))
                if services:
                    speed, _ = _station_scroll_settings(screen)
                    prepared = screen.get("rail_presentation") or {}
                    travel = prepared.get("calling_travel_seconds", screen.get("_calling_travel_seconds"))
                    if travel is None:
                        travel = rail_calling_timing(
                            services, speed, font_width=WEATHER_FONT_WIDTH
                        )[0]
                    marquee_cycle = travel + CALLING_MARQUEE_PAUSE_SECONDS
                    boundaries.append(_next_periodic_boundary(
                        calling_elapsed, (0.0, travel, marquee_cycle), marquee_cycle
                    ))
            return max(0.05, min(boundaries))
        return _header_next_boundary_seconds(phase, screen.get("weather"))

    def _departures_calling_moving(self, screen, phase, calling_seconds=RAIL_CALLING_SECONDS,
                                   summary_seconds=RAIL_SUMMARY_SECONDS):
        if rail_phase(phase, summary_seconds, calling_seconds) != "calling":
            return False
        services = screen.get("services") or ()
        scroll_speed, _ = _station_scroll_settings(screen)
        for service_index in (0,):
            if service_index >= len(services):
                continue
            prepared = screen.get("rail_presentation") or {}
            travel_seconds = prepared.get("calling_travel_seconds", screen.get("_calling_travel_seconds"))
            if travel_seconds is None:
                travel_seconds = rail_calling_timing(
                    (services[service_index],),
                    scroll_speed,
                    font_width=WEATHER_FONT_WIDTH,
                )[0]
            cycle_seconds = travel_seconds + CALLING_MARQUEE_PAUSE_SECONDS
            within_cycle = rail_marquee_elapsed(phase, summary_seconds, calling_seconds) % cycle_seconds
            if within_cycle < travel_seconds:
                return True
        return False

    def _departures_rows_moving(self, screen, phase, calling_seconds=RAIL_CALLING_SECONDS,
                                summary_seconds=RAIL_SUMMARY_SECONDS):
        if not MATRIX_RAIL_ROWS_SCROLL:
            return False
        if rail_phase(phase, summary_seconds, calling_seconds) != "calling":
            return False
        services = screen.get("services") or ()
        start, progress, reset_progress = departure_scroll_state(
            rail_marquee_elapsed(phase, summary_seconds, calling_seconds),
            max(0, len(services) - 1),
            screen.get("upcoming_train_pause_seconds", 2),
            visible_rows=2,
        )
        return progress > 0 or (reset_progress is not None and reset_progress > 0)

    def _record_animation_update(self, scene, changed, duration, animation_class=None):
        self._stats_animation_ticks += 1
        self._stats_update_total += duration
        self._stats_update_max = max(self._stats_update_max, duration)
        if scene == "todoist":
            self._stats_todoist_ticks += 1
            if changed:
                self._stats_todoist_changed += 1
        elif scene == "rail":
            self._stats_rail_ticks += 1
            if changed:
                self._stats_rail_changed += 1
        if animation_class in self._stats_animation_classes:
            counters = self._stats_animation_classes[animation_class]
            counters["ticks"] += 1
            counters["update_total"] += duration
            counters["update_max"] = max(counters["update_max"], duration)
            if changed:
                counters["changed"] += 1

    def _refresh(self, animation_class=None):
        """Present one changed scene according to the issue #70 test mode."""
        self._stats_changes += 1

        # With auto-refresh enabled, mutating displayio objects is sufficient.
        # Calling refresh() here would make this mode no longer a clean test.
        if self.presentation_mode == "auto_refresh":
            self._maybe_report_stats()
            return True

        self._stats_refresh_attempts += 1
        target = None if self.presentation_mode == "immediate" else MATRIX_REFRESH_FPS
        heap_before = (
            self._heap_free() if animation_class == "departures_calling" else None
        )
        refresh_started = time.monotonic()
        refreshed = self.display.refresh(target_frames_per_second=target)
        now = time.monotonic()
        if heap_before is not None:
            heap_after = self._heap_free()
            if heap_after is not None:
                self._stats_rail_refresh_heap_gain_max = max(
                    self._stats_rail_refresh_heap_gain_max,
                    heap_after - heap_before,
                )
        if animation_class in self._stats_animation_classes:
            counters = self._stats_animation_classes[animation_class]
            refresh_duration = now - refresh_started
            counters["refresh_total"] += refresh_duration
            counters["refresh_max"] = max(counters["refresh_max"], refresh_duration)
        if refreshed:
            self._stats_refresh_successes += 1
            refresh_duration = now - refresh_started
            self._stats_refresh_total += refresh_duration
            self._stats_refresh_max = max(self._stats_refresh_max, refresh_duration)
            self._record_success_interval(now)
        else:
            self._stats_refresh_failures += 1
            self._refresh_misses += 1
            if self._refresh_misses % 20 == 0:
                print("DISPLAY REFRESH DEADLINE MISSED count={}".format(self._refresh_misses))
        self._maybe_report_stats()
        return refreshed

    def _present(self, group):
        """Publish one fully-built frame to the matrix."""
        self._attach_brightness_overlay(group, bring_to_front=True)
        self.display.root_group = group
        # Pace frame publication through framebufferio. This waits for the
        # display refresh scheduler rather than swapping a frame mid-cycle.
        self._refresh()

    def show_loading(self, title="UPCOMING", message="Loading...", clock_time="--:--"):
        """Show a cheap transition card before building a heavy screen."""
        import displayio

        group = displayio.Group()
        title = _clip(title, 30)
        message = _clip(message, 30)
        message_x = max(0, (DISPLAY_WIDTH - len(message) * WEATHER_FONT_WIDTH) // 2)
        self._label(group, title, 0xFFAA00, 0, 3)
        self._label(group, message, 0xFFFFFF, message_x, 18)
        self._label(group, clock_time, 0xFFAA00, CLOCK_X, 3)
        self._present(group)

    def show_diagnostic(self, color):
        """Fill the complete physical matrix with one moderate test colour."""
        import displayio

        bitmap = displayio.Bitmap(DISPLAY_WIDTH, 32, 1)
        palette = displayio.Palette(1)
        palette[0] = int(color)
        group = displayio.Group()
        group.append(displayio.TileGrid(bitmap, pixel_shader=palette))
        self._present(group)
        print("DIAGNOSTIC 0x{:06X}".format(int(color)))

    def _rail_service(self, group, service, color, x_offset, y, right_edge, ordinal=1):
        ordinal_text, time_text, destination, platform, status = _rail_columns(service, ordinal)
        status_x = _right_aligned_x(status, right_edge) if status else int(right_edge)
        platform_width = min(RAIL_PLATFORM_WIDTH, len(platform) * WEATHER_FONT_WIDTH)
        platform_x = RAIL_PLATFORM_X
        if status and status_x < platform_x + platform_width + HEADER_GAP:
            platform_x = max(RAIL_DESTINATION_X, status_x - platform_width - HEADER_GAP)
        destination_width = max(0, platform_x - HEADER_GAP - RAIL_DESTINATION_X)
        self._label(group, ordinal_text, color, RAIL_ORDINAL_X + x_offset, y)
        self._label(group, time_text, color, RAIL_TIME_X + x_offset, y)
        self._label(group, _fit_text_pixels(destination, destination_width), color, RAIL_DESTINATION_X + x_offset, y)
        self._label(group, platform, color, platform_x + x_offset, y)
        if status:
            self._label(group, status, color, status_x + x_offset, y)

    def _rail(self, group, screen, phase):
        import displayio

        services = screen.get("services") or []
        rail_right_edge = _header_content_right(screen)
        calling_seconds = screen.get("calling_seconds", RAIL_CALLING_SECONDS)
        summary_seconds = screen.get("summary_seconds", RAIL_SUMMARY_SECONDS)
        state = rail_phase(phase, summary_seconds, calling_seconds)
        rows = rail_rows(services, phase, calling_seconds, summary_seconds)
        self._rail_calling_labels = []
        self._rail_departure_rows = []
        calling_group = None
        calling_label_state = None
        fixed_group = displayio.Group() if state == "calling" else group
        for row_index, (row_kind, service) in enumerate(rows):
            y = RAIL_ROW_Y[row_index]
            if row_kind == "header":
                self._label(group, "DEPARTURES", 0xFFAA00, 0, y)
            elif row_kind == "service" and service is not None:
                if state == "calling" and row_index >= 2:
                    continue
                if state == "calling":
                    ordinal = 1 if row_index == 0 else row_index
                else:
                    first_service_row = 0 if rows and rows[0][0] == "service" else 1
                    ordinal = row_index - first_service_row + 1
                color = 0xFF3300 if service.get("cancelled") else 0xFFFFFF
                self._rail_service(fixed_group, service, color, 0, y, rail_right_edge, ordinal)
            elif row_kind == "calling":
                calling_group = displayio.Group()
                presentation = screen.get("rail_presentation") or {}
                calling = presentation.get("calling_text") or calling_text(service)
                stations = calling[len(CALLING_LABEL):] if calling.startswith(CALLING_LABEL) else calling
                first = self._calling_label_group(
                    service, y, presentation.get("calling_segments")
                )
                calling_group.append(first)
                self._mask(calling_group, 0, y - 3, len(CALLING_LABEL) * WEATHER_FONT_WIDTH, 8)
                prefix = self._label(calling_group, CALLING_LABEL, 0xFFAA00, 0, y)
                calling_label_state = {
                    "prefix": prefix,
                    "first": first,
                    "text": calling,
                    "station_width": presentation.get(
                        "calling_station_width_px", len(stations) * WEATHER_FONT_WIDTH
                    ),
                }
        if state == "calling":
            # The top service and its calling row remain fixed. Cycle all
            # later services through the two lower physical rows.
            for index, service in enumerate(services[1:]):
                row_group = displayio.Group()
                color = 0xFF3300 if service.get("cancelled") else 0xFFFFFF
                self._rail_service(row_group, service, color, 0, 0, rail_right_edge, index + 2)
                row_group.y = RAIL_ROW_Y[-1] + 8
                group.append(row_group)
                self._rail_departure_rows.append(row_group)
            # Label coordinates are baselines: glyphs start three pixels
            # above them. Hide moving rows above the lower viewport, then
            # draw both fixed rows on top so outgoing glyphs cannot overlap.
            self._mask(
                group,
                0,
                0,
                DISPLAY_WIDTH,
                RAIL_ROW_Y[2] - 3,
            )
            if calling_group is not None:
                fixed_group.append(calling_group)
                self._rail_calling_labels.append(calling_label_state)
            group.append(fixed_group)
        self._rail_phase = state

    def _rail_cache_matches(self, screen):
        return (
            self._rail_group is not None
            and self._rail_services == screen.get("services")
            and self._rail_title == screen.get("title")
            and self._rail_stale == bool(screen.get("stale"))
            and _rail_weather_key(self._rail_weather) == _rail_weather_key(screen.get("weather"))
        )

    def _build_rail_scene(self, screen, clock_time, phase):
        """Build both departures layouts once; phase changes only swap roots."""
        import displayio

        scenes = {}
        calling_seconds = screen.get("calling_seconds", RAIL_CALLING_SECONDS)
        summary_seconds = screen.get("summary_seconds", RAIL_SUMMARY_SECONDS)
        scene_phases = (0,) if summary_seconds <= 0 else (0, summary_seconds)
        for scene_phase in scene_phases:
            root = displayio.Group()
            self._rail(root, screen, scene_phase)
            calling_labels = self._rail_calling_labels
            departure_rows = self._rail_departure_rows

            # Departures owns all four physical rows. The generic header mask
            # used by other screens would cover row 1.
            clock_group = displayio.Group()
            clock_label = self._label(clock_group, "", 0xFFAA00, CLOCK_X, 3)
            weather_group = displayio.Group()
            if isinstance(screen.get("weather"), dict):
                self._header_weather(weather_group, screen.get("weather"), 0)
            root.append(clock_group)
            root.append(weather_group)
            scenes[rail_phase(scene_phase, summary_seconds, calling_seconds)] = {
                "group": root,
                "calling_labels": calling_labels,
                "departure_rows": departure_rows,
                "clock_group": clock_group,
                "clock_label": clock_label,
                "weather_group": weather_group,
            }

        self._rail_scenes = scenes
        self._rail_services = screen.get("services")
        self._rail_title = screen.get("title")
        self._rail_stale = bool(screen.get("stale"))
        self._rail_weather = screen.get("weather")
        self._select_rail_scene(phase, calling_seconds, summary_seconds)

    def _select_rail_scene(self, phase, calling_seconds=RAIL_CALLING_SECONDS,
                           summary_seconds=RAIL_SUMMARY_SECONDS):
        """Select a cached summary/calling layout without rebuilding labels."""
        state = rail_phase(phase, summary_seconds, calling_seconds)
        scene = self._rail_scenes[state]
        self._rail_group = scene["group"]
        self._rail_calling_labels = scene["calling_labels"]
        self._rail_departure_rows = scene["departure_rows"]
        self._rail_clock_group = scene["clock_group"]
        self._rail_clock_label = scene["clock_label"]
        self._rail_weather_group = scene["weather_group"]
        self._rail_phase = state

    def _update_rail_scene(self, screen, clock_time, phase):
        """Update only the calling-at marquee and rotating header item."""
        changed = False
        scroll_speed, scroll_gap = _station_scroll_settings(screen)
        calling_seconds = screen.get("calling_seconds", RAIL_CALLING_SECONDS)
        summary_seconds = screen.get("summary_seconds", RAIL_SUMMARY_SECONDS)
        for labels in self._rail_calling_labels:
            calling_x = calling_marquee_x(
                labels["text"],
                rail_marquee_elapsed(phase, summary_seconds, calling_seconds),
                display_width=DISPLAY_WIDTH,
                font_width=WEATHER_FONT_WIDTH,
                speed=scroll_speed,
                gap=scroll_gap,
                stop_at_end=True,
                station_width=labels["station_width"],
            )
            first_x = int(calling_x)
            if labels["first"].x != first_x:
                labels["first"].x = first_x
                changed = True

        services = screen.get("services") or ()
        hidden_y = RAIL_ROW_Y[-1] + 8
        row_step = RAIL_ROW_Y[3] - RAIL_ROW_Y[2]
        if MATRIX_RAIL_ROWS_SCROLL:
            start, progress, reset_progress = departure_scroll_state(
                rail_marquee_elapsed(phase, summary_seconds, calling_seconds),
                max(0, len(services) - 1),
                screen.get("upcoming_train_pause_seconds", 2),
                visible_rows=2,
            )
            for index, row_group in enumerate(self._rail_departure_rows):
                if reset_progress is None:
                    row_y = hidden_y + index * row_step
                elif reset_progress > 0:
                    if index < 2:
                        row_y = RAIL_ROW_Y[2] + 2 * row_step - int(
                            reset_progress * 2 * row_step
                        ) + index * row_step
                    else:
                        row_y = hidden_y + index * row_step
                elif start <= index <= start + 2:
                    row_y = RAIL_ROW_Y[2] + (index - start) * row_step - int(
                        progress * row_step
                    )
                else:
                    row_y = hidden_y + index * row_step
                if row_group.y != row_y:
                    row_group.y = row_y
                    changed = True
        else:
            for index, row_group in enumerate(self._rail_departure_rows):
                row_y = (
                    RAIL_ROW_Y[2] + index * row_step
                    if index < 2
                    else hidden_y + index * row_step
                )
                if row_group.y != row_y:
                    row_group.y = row_y
                    changed = True

        if self._rail_clock_label.text != clock_time:
            self._rail_clock_label.text = clock_time
            changed = True
        item, offset = _header_item_state(phase, screen.get("weather"))
        clock_x = offset if item == "clock" else DISPLAY_WIDTH
        weather_x = offset if item == "weather" else DISPLAY_WIDTH
        if self._rail_clock_group.x != clock_x:
            self._rail_clock_group.x = clock_x
            changed = True
        if self._rail_weather_group.x != weather_x:
            self._rail_weather_group.x = weather_x
            changed = True
        return changed

    def _show_rail(self, screen, clock_time, phase):
        """Render departures with a persistent scene and live calling marquee."""
        calling_seconds = screen.get("calling_seconds", RAIL_CALLING_SECONDS)
        summary_seconds = screen.get("summary_seconds", RAIL_SUMMARY_SECONDS)
        state = rail_phase(phase, summary_seconds, calling_seconds)
        if not self._rail_cache_matches(screen):
            self._build_rail_scene(screen, clock_time, phase)
        elif self._rail_phase != state:
            self._select_rail_scene(phase, calling_seconds, summary_seconds)
        update_heap_before = self._heap_free()
        update_started = time.monotonic()
        changed = self._update_rail_scene(screen, clock_time, phase)
        update_duration = time.monotonic() - update_started
        if update_duration > 0.1 and update_heap_before is not None:
            update_heap_after = self._heap_free()
            if update_heap_after is not None:
                self._stats_rail_update_heap_gain_max = max(
                    self._stats_rail_update_heap_gain_max,
                    update_heap_after - update_heap_before,
                )
        self._attach_brightness_overlay(self._rail_group)
        if self.display.root_group is not self._rail_group:
            self.display.root_group = self._rail_group
            changed = True
        animation_class = self._animation_class(screen, phase)
        self._record_animation_update(
            "rail",
            changed,
            update_duration,
            animation_class,
        )
        if changed:
            self._refresh(animation_class)

    def _queues(self, group, screen, phase):
        rides = screen.get("rides") or []
        if not rides:
            self._label(group, "Queue data unavailable", 0xFFFFFF, 0, QUEUE_FIRST_Y)
        else:
            start, progress = queue_scroll_state(phase, len(rides))
            row_count = QUEUE_VISIBLE_ROWS + (1 if progress > 0 else 0)
            y_offset = int(progress * QUEUE_ROW_HEIGHT)
            for slot in range(row_count):
                ride_index = start + slot
                if ride_index >= len(rides):
                    break
                ride = rides[ride_index]
                name, state = _queue_parts(ride)
                state_x = _right_aligned_x(state, DISPLAY_WIDTH)
                y = QUEUE_FIRST_Y + slot * QUEUE_ROW_HEIGHT - y_offset
                color = 0xFFFFFF if ride.get("open") else 0xFF3300
                self._label(group, _left_text(name, max(0, state_x - HEADER_GAP)), color, 0, y)
                self._label(group, state, color, state_x, y)
        self._header_mask(group)
        self._label(group, _clip(screen.get("title") or "THORPE PARK", 30), 0xFFAA00, 0, 3)

    def _calendar(self, group, screen, phase, clock_date=""):
        events, visible, start, progress = _agenda_state(screen, phase)
        if not events:
            self._label(group, "No upcoming events", 0xFFFFFF, 0, AGENDA_FIRST_Y)
        else:
            row_count = min(len(events) - start, visible * 2 if progress > 0 else visible)
            y_offset = int(progress * visible * AGENDA_ROW_HEIGHT)
            for slot in range(max(0, row_count)):
                event_index = start + slot
                if event_index >= len(events):
                    break
                event = events[event_index]
                when, title = calendar_row_parts(event)
                y = AGENDA_FIRST_Y + slot * AGENDA_ROW_HEIGHT - y_offset
                due = todoist_due_label(event, clock_date) if screen.get("source") == "todoist" else ""
                if due:
                    due_x = _right_aligned_x(due, DISPLAY_WIDTH)
                    title_width = max(0, due_x - HEADER_GAP - AGENDA_TITLE_X)
                    title_chars = max(1, title_width // 5)
                    title_x = AGENDA_TITLE_X + agenda_marquee_x(
                        title,
                        phase,
                        visible_chars=title_chars,
                        font_width=5,
                        speed=TODOIST_MARQUEE_SPEED,
                        pause_seconds=TODOIST_MARQUEE_PAUSE_SECONDS,
                    )
                    self._label(group, title, 0xFFFFFF, title_x, y)
                    # Clip the moving title before the fixed due/event label
                    # is painted, so long text cannot overlap it.
                    self._mask(
                        group,
                        due_x - HEADER_GAP,
                        y - 3,
                        DISPLAY_WIDTH - due_x + HEADER_GAP,
                        AGENDA_ROW_HEIGHT,
                    )
                else:
                    self._label(group, title, 0xFFFFFF, agenda_title_marquee_x(title, phase), y)
                self._mask(group, 0, y - 3, AGENDA_TITLE_X, AGENDA_ROW_HEIGHT)
                self._label(group, when, 0xFFFFFF, 0, y)
                if due:
                    self._label(group, due, 0xFFFFFF, due_x, y)
        self._header_mask(group)
        self._label(group, _clip(screen.get("title") or "UPCOMING", 30), 0xFFAA00, 0, 3)

    def _flash(self, group, screen, phase=0):
        """A large clock continuously leads the complete reminder text from right to left."""
        import displayio
        motion = displayio.Group(x=reminder_scroll_x(screen, phase))
        bitmap = displayio.Bitmap(REMINDER_CLOCK_SIZE, REMINDER_CLOCK_SIZE, 2)
        palette = displayio.Palette(2)
        palette.make_transparent(0)
        palette[1] = 0xFFAA00
        for x in range(REMINDER_CLOCK_SIZE):
            for y in range(REMINDER_CLOCK_SIZE):
                if reminder_clock_pixel(x, y):
                    bitmap[x, y] = 1
        motion.append(displayio.TileGrid(bitmap, pixel_shader=palette, x=0, y=1))
        self._scaled_label(motion, str(screen.get("label") or ""),
                           0xFFFFFF, REMINDER_TEXT_X, 5, scale=REMINDER_TEXT_SCALE)
        group.append(motion)
        return motion

    def _show_flash(self, screen, phase):
        import displayio
        key = (screen.get("id"), screen.get("label"), screen.get("duration_seconds"))
        changed = False
        if getattr(self, "_flash_key", None) != key:
            self._flash_group = displayio.Group()
            self._flash_motion = self._flash(self._flash_group, screen, phase)
            self._flash_key = key
            changed = True
        x = reminder_scroll_x(screen, phase)
        if self._flash_motion.x != x:
            self._flash_motion.x = x
            changed = True
        self._attach_brightness_overlay(self._flash_group)
        if self.display.root_group is not self._flash_group:
            self.display.root_group = self._flash_group
            changed = True
        if changed:
            self._refresh(self._animation_class(screen, phase))

    def _todoist_cache_matches(self, screen, clock_date):
        weather = screen.get("weather")
        weather_icon = weather.get("icon") if isinstance(weather, dict) else None
        weather_temp = weather.get("temperature_c") if isinstance(weather, dict) else None
        weather_stale = bool(weather.get("stale")) if isinstance(weather, dict) else False
        return (
            self._todoist_group is not None
            and self._todoist_events == screen.get("events")
            and self._todoist_clock_date == clock_date
            and self._todoist_title == screen.get("title")
            and self._todoist_stale == bool(screen.get("stale"))
            and self._todoist_viewport_size == max(1, int(screen.get("viewport_size") or AGENDA_VISIBLE_ROWS))
            and self._todoist_page_step == max(1, int(screen.get("page_step") or 1))
            and self._todoist_page_seconds == (screen.get("page_seconds") or 5)
            and self._todoist_weather_icon == weather_icon
            and self._todoist_weather_temp == weather_temp
            and self._todoist_weather_stale == weather_stale
        )

    def _build_todoist_scene(self, screen, clock_time, clock_date):
        """Build the Todoist scene once; animation mutates only child positions."""
        import displayio

        root = displayio.Group()
        events = screen.get("events") or ()
        rows = []

        if not events:
            self._label(root, "No upcoming events", 0xFFFFFF, 0, AGENDA_FIRST_Y)
        else:
            for event in events:
                row_group = displayio.Group()
                title_group = displayio.Group()
                when, title = calendar_row_parts(event)
                due = todoist_due_label(event, clock_date)
                due_x = _right_aligned_x(due, DISPLAY_WIDTH) if due else DISPLAY_WIDTH
                title_width = max(0, due_x - HEADER_GAP - AGENDA_TITLE_X) if due else DISPLAY_WIDTH - AGENDA_TITLE_X
                visible_chars = max(1, title_width // WEATHER_FONT_WIDTH)

                for chunk_start in range(0, max(1, len(title)), 24):
                    self._label(
                        title_group,
                        title[chunk_start:chunk_start + 24],
                        0xFFFFFF,
                        chunk_start * WEATHER_FONT_WIDTH,
                        0,
                    )
                row_group.append(title_group)

                # Masks are fixed children of the row. Only title_group.x and
                # row_group.y change while scrolling, so no per-frame Bitmap,
                # Palette, Label or Group allocation is needed.
                if due:
                    self._mask(
                        row_group,
                        due_x - HEADER_GAP,
                        -3,
                        DISPLAY_WIDTH - due_x + HEADER_GAP,
                        AGENDA_ROW_HEIGHT,
                    )
                self._mask(row_group, 0, -3, AGENDA_TITLE_X, AGENDA_ROW_HEIGHT)
                self._label(row_group, when, 0xFFFFFF, 0, 0)
                if due:
                    due_color = 0xFF3300 if due == "OVERDUE" else 0xFFFFFF
                    self._label(row_group, due, due_color, due_x, 0)

                row_group.y = 64
                root.append(row_group)
                rows.append((row_group, title_group, title, visible_chars))

        self._header_mask(root)
        self._label(root, _clip(screen.get("title") or "UPCOMING", 30), 0xFFAA00, 0, 3)
        if screen.get("stale"):
            self._label(root, "STALE", 0xFF3300, STALE_X, 3)

        self._mask(root, HEADER_SLOT_X, 0, HEADER_SLOT_WIDTH, 8)
        clock_group = displayio.Group()
        clock_label = self._label(clock_group, clock_time, 0xFFAA00, CLOCK_X, 3)
        root.append(clock_group)

        weather_group = displayio.Group()
        if isinstance(screen.get("weather"), dict):
            self._header_weather(weather_group, screen.get("weather"), 0)
        root.append(weather_group)

        weather = screen.get("weather")
        self._todoist_group = root
        self._todoist_rows = rows
        self._todoist_events = screen.get("events")
        self._todoist_clock_date = clock_date
        self._todoist_title = screen.get("title")
        self._todoist_stale = bool(screen.get("stale"))
        self._todoist_viewport_size = max(1, int(screen.get("viewport_size") or AGENDA_VISIBLE_ROWS))
        self._todoist_page_step = max(1, int(screen.get("page_step") or 1))
        self._todoist_page_seconds = screen.get("page_seconds") or 5
        last_start = max(0, len(rows) - self._todoist_viewport_size)
        page_starts = list(range(0, last_start + 1, self._todoist_page_step))
        if page_starts[-1] != last_start:
            page_starts.append(last_start)
        page_durations = []
        for start in page_starts:
            longest_scroll = 0.0
            stop = min(len(rows), start + self._todoist_viewport_size)
            for row_index in range(start, stop):
                row = rows[row_index]
                longest_scroll = max(
                    longest_scroll,
                    self._todoist_title_scroll_seconds(row[2], row[3]),
                )
            page_durations.append(
                longest_scroll
                + (TODOIST_MARQUEE_PAUSE_SECONDS if longest_scroll else 0.0)
                + max(0.0, float(self._todoist_page_seconds or 0))
            )
        self._todoist_page_starts = tuple(page_starts)
        self._todoist_page_durations = tuple(page_durations)
        self._todoist_weather_icon = weather.get("icon") if isinstance(weather, dict) else None
        self._todoist_weather_temp = weather.get("temperature_c") if isinstance(weather, dict) else None
        self._todoist_weather_stale = bool(weather.get("stale")) if isinstance(weather, dict) else False
        self._todoist_clock_group = clock_group
        self._todoist_clock_label = clock_label
        self._todoist_weather_group = weather_group

    def _todoist_title_scroll_seconds(self, title, visible_chars):
        """Return the one-way scroll time needed to reveal a Todoist title."""
        visible_chars = max(1, int(visible_chars or 1))
        overflow = max(0, (len(str(title or "")) - visible_chars) * WEATHER_FONT_WIDTH)
        return overflow / max(1.0, float(TODOIST_MARQUEE_SPEED))

    def _todoist_page_transition_at(self, start):
        """Return the dwell time for the Todoist window at ``start``."""
        for index in range(len(self._todoist_page_starts)):
            if self._todoist_page_starts[index] == start:
                return self._todoist_page_durations[index]

        try:
            minimum_page_seconds = max(0.0, float(self._todoist_page_seconds or 0))
        except (TypeError, ValueError):
            minimum_page_seconds = 0.0
        longest_scroll = 0.0
        stop = min(len(self._todoist_rows), max(0, start) + self._todoist_viewport_size)
        for row_index in range(max(0, start), stop):
            row = self._todoist_rows[row_index]
            longest_scroll = max(
                longest_scroll,
                self._todoist_title_scroll_seconds(row[2], row[3]),
            )
        return (
            longest_scroll
            + (TODOIST_MARQUEE_PAUSE_SECONDS if longest_scroll else 0.0)
            + minimum_page_seconds
        )

    def _todoist_page_slide_active(self, phase):
        if len(self._todoist_rows) <= self._todoist_viewport_size:
            return False
        try:
            remaining = max(0.0, float(phase or 0))
        except (TypeError, ValueError):
            return False
        starts = self._todoist_page_starts
        for index in range(max(0, len(starts) - 1)):
            start = starts[index]
            remaining -= self._todoist_page_transition_at(start)
            if remaining < AGENDA_SLIDE_SECONDS:
                return remaining > 0.0
            remaining -= AGENDA_SLIDE_SECONDS
        return False

    def _todoist_titles_moving(self, phase):
        try:
            phase = max(0.0, float(phase or 0))
        except (TypeError, ValueError):
            phase = 0.0
        visible = self._todoist_viewport_size
        if not visible:
            return False
        remaining = phase
        starts = self._todoist_page_starts
        for index in range(len(starts)):
            start = starts[index]
            duration = self._todoist_page_transition_at(start)
            if remaining <= duration or index == len(starts) - 1:
                stop = min(len(self._todoist_rows), start + visible)
                for row_index in range(start, stop):
                    row = self._todoist_rows[row_index]
                    if remaining < self._todoist_title_scroll_seconds(row[2], row[3]):
                        return True
                return False
            remaining -= duration
            if remaining < AGENDA_SLIDE_SECONDS:
                return False
            remaining -= AGENDA_SLIDE_SECONDS
        return False

    def _todoist_title_x(self, title, phase, visible_chars):
        """Scroll once to the final title position instead of looping."""
        visible_chars = max(1, int(visible_chars or 1))
        overflow = max(0, (len(str(title or "")) - visible_chars) * WEATHER_FONT_WIDTH)
        if overflow <= 0:
            return AGENDA_TITLE_X
        try:
            phase = max(0.0, float(phase or 0))
        except (TypeError, ValueError):
            phase = 0.0
        offset = min(
            overflow,
            int(phase * max(1.0, float(TODOIST_MARQUEE_SPEED)) + 1e-9),
        )
        return AGENDA_TITLE_X - offset

    def _update_todoist_scene(self, screen, clock_time, phase):
        """Move cached Todoist groups using page-local animation phases."""
        changed = False
        visible = self._todoist_viewport_size
        event_count = len(self._todoist_rows)
        try:
            phase = max(0.0, float(phase or 0))
        except (TypeError, ValueError):
            phase = 0.0

        start = 0
        progress = 0.0
        page_phase = phase
        sliding_from = None

        if event_count > visible:
            remaining = phase
            starts = self._todoist_page_starts
            for index in range(len(starts)):
                candidate = starts[index]
                window_duration = self._todoist_page_transition_at(candidate)
                if remaining <= window_duration or index == len(starts) - 1:
                    start = candidate
                    page_phase = remaining
                    break
                remaining -= window_duration
                if remaining <= AGENDA_SLIDE_SECONDS + 1e-9:
                    if remaining >= AGENDA_SLIDE_SECONDS - 1e-9:
                        remaining = AGENDA_SLIDE_SECONDS
                    else:
                        start = candidate
                        progress = max(0.0, remaining / AGENDA_SLIDE_SECONDS)
                        page_phase = None
                        sliding_from = candidate
                        break
                remaining -= AGENDA_SLIDE_SECONDS

        y_offset = int(progress * self._todoist_page_step * AGENDA_ROW_HEIGHT + 1e-9)

        for index in range(event_count):
            row = self._todoist_rows[index]
            row_group, title_group, title, visible_chars = row
            if progress > 0 and start <= index < start + visible + self._todoist_page_step:
                y = AGENDA_FIRST_Y + (index - start) * AGENDA_ROW_HEIGHT - y_offset
            elif progress <= 0 and start <= index < start + visible:
                y = AGENDA_FIRST_Y + (index - start) * AGENDA_ROW_HEIGHT
            else:
                y = 64
            if row_group.y != y:
                row_group.y = y
                changed = True

            if progress > 0:
                if sliding_from is not None and index < sliding_from + visible:
                    title_phase = self._todoist_title_scroll_seconds(title, visible_chars)
                else:
                    title_phase = 0.0
            elif start <= index < start + visible:
                title_phase = page_phase
            else:
                title_phase = 0.0

            title_x = self._todoist_title_x(title, title_phase, visible_chars)
            if title_group.x != title_x:
                title_group.x = title_x
                changed = True

        if self._todoist_clock_label.text != clock_time:
            self._todoist_clock_label.text = clock_time
            changed = True

        item, offset = _header_item_state(phase, screen.get("weather"))
        clock_x = offset if item == "clock" else DISPLAY_WIDTH
        weather_x = offset if item == "weather" else DISPLAY_WIDTH
        if self._todoist_clock_group.x != clock_x:
            self._todoist_clock_group.x = clock_x
            changed = True
        if self._todoist_weather_group.x != weather_x:
            self._todoist_weather_group.x = weather_x
            changed = True
        return changed

    def _show_todoist(self, screen, clock_time, clock_date, phase):
        """Render Todoist with a persistent scene graph and coordinate-only animation."""
        if not self._todoist_cache_matches(screen, clock_date):
            self._build_todoist_scene(screen, clock_time, clock_date)

        update_started = time.monotonic()
        changed = self._update_todoist_scene(screen, clock_time, phase)
        self._attach_brightness_overlay(self._todoist_group)
        if self.display.root_group is not self._todoist_group:
            self.display.root_group = self._todoist_group
            changed = True
        animation_class = self._animation_class(screen, phase)
        self._record_animation_update(
            "todoist",
            changed,
            time.monotonic() - update_started,
            animation_class,
        )
        if changed:
            self._refresh(animation_class)

    def _steam_train_cache_matches(self, screen):
        try:
            speed = max(8.0, min(80.0, float(screen.get("animation_speed") or 24)))
        except (TypeError, ValueError):
            speed = 24.0
        return (
            self._steam_train_group is not None
            and self._steam_train_words == str(screen.get("words") or "")
            and self._steam_train_speed == speed
        )

    def _build_steam_train_scene(self, screen):
        import displayio

        root = displayio.Group()
        motion = displayio.Group(x=0, y=STEAM_TRAIN_VERTICAL_OFFSET)
        bitmap = displayio.Bitmap(STEAM_TRAIN_WIDTH, STEAM_TRAIN_HEIGHT, 5)
        palette = displayio.Palette(5)
        palette[0] = 0x000000
        palette.make_transparent(0)
        palette[1] = 0xFFFFFF
        palette[2] = 0xFFAA00
        palette[3] = 0xAAAAAA
        palette[4] = 0xFF3300

        def fill_rect(x, y, width, height, color):
            for py in range(max(0, y), min(STEAM_TRAIN_HEIGHT, y + height)):
                for px in range(max(0, x), min(STEAM_TRAIN_WIDTH, x + width)):
                    bitmap[px, py] = color

        fill_rect(4, 9, 29, 9, 1)
        fill_rect(30, 4, 16, 14, 1)
        fill_rect(8, 2, 7, 7, 3)
        fill_rect(6, 1, 11, 2, 3)
        fill_rect(28, 2, 20, 3, 2)
        fill_rect(0, 14, 6, 3, 2)
        fill_rect(16, 6, 16, 3, 1)
        # Cab window stays transparent/black.
        fill_rect(34, 6, 7, 6, 0)

        wheel_points = (
            (-2, -3), (-1, -3), (0, -3), (1, -3), (2, -3),
            (-3, -2), (3, -2), (-3, -1), (3, -1),
            (-3, 0), (0, 0), (3, 0),
            (-3, 1), (3, 1), (-3, 2), (3, 2),
            (-2, 3), (-1, 3), (0, 3), (1, 3), (2, 3),
        )
        for center_x in (11, 34, 43):
            for dx, dy in wheel_points:
                px = center_x + dx
                py = 20 + dy
                if 0 <= px < STEAM_TRAIN_WIDTH and 0 <= py < STEAM_TRAIN_HEIGHT:
                    bitmap[px, py] = 4

        motion.append(displayio.TileGrid(bitmap, pixel_shader=palette, x=0, y=3))
        words = str(screen.get("words") or "")
        if words:
            self._scaled_label(
                motion,
                words,
                0xFFAA00,
                STEAM_TRAIN_WIDTH + STEAM_TRAIN_TEXT_GAP,
                5,
            )
        root.append(motion)

        try:
            speed = max(8.0, min(80.0, float(screen.get("animation_speed") or 24)))
        except (TypeError, ValueError):
            speed = 24.0
        self._steam_train_group = root
        self._steam_train_motion_group = motion
        self._steam_train_words = words
        self._steam_train_speed = speed

    def _update_steam_train_scene(self, phase):
        if self._steam_train_motion_group is None:
            return False
        try:
            elapsed = max(0.0, float(phase or 0))
        except (TypeError, ValueError):
            elapsed = 0.0
        next_x = max(0, DISPLAY_WIDTH - int(elapsed * self._steam_train_speed))
        if self._steam_train_motion_group.x == next_x:
            return False
        self._steam_train_motion_group.x = next_x
        return True

    def _show_steam_train(self, screen, phase):
        if not self._steam_train_cache_matches(screen):
            self._build_steam_train_scene(screen)
        update_started = time.monotonic()
        changed = self._update_steam_train_scene(phase)
        self._attach_brightness_overlay(self._steam_train_group)
        if self.display.root_group is not self._steam_train_group:
            self.display.root_group = self._steam_train_group
            changed = True
        animation_class = self._animation_class(screen, phase)
        self._record_animation_update(
            "steam_train",
            changed,
            time.monotonic() - update_started,
            animation_class,
        )
        if changed:
            self._refresh(animation_class)

    def _weekly_weather(self, group, screen):
        import displayio

        layout = _weekly_weather_layout(screen.get("days") or [])
        if not layout:
            text = "Weather unavailable"
            x = max(0, (DISPLAY_WIDTH - len(text) * WEATHER_FONT_WIDTH) // 2)
            self._label(group, text, 0xAAAAAA, x, 18)
            return

        stale = bool(screen.get("stale"))
        text_color = 0xAAAAAA if stale else 0xFFFFFF
        weekday_color = 0x777777 if stale else 0xFFAA00
        for item in layout:
            self._label(group, item["weekday"], weekday_color, item["weekday_x"], WEATHER_HEADING_BASELINE_Y)
            bitmap = displayio.Bitmap(item["icon_width"], 14, 2)
            palette = displayio.Palette(2)
            palette[0] = 0x000000
            palette.make_transparent(0)
            palette[1] = _weather_rgb(item["icon_name"], stale)
            for y, row in enumerate(item["icon_rows"]):
                for x, pixel in enumerate(row):
                    if pixel == "#":
                        for dx in range(WEEKLY_WEATHER_ICON_SCALE):
                            for dy in range(WEEKLY_WEATHER_ICON_SCALE):
                                bitmap[x * WEEKLY_WEATHER_ICON_SCALE + dx, y * WEEKLY_WEATHER_ICON_SCALE + dy] = 1
            group.append(displayio.TileGrid(
                bitmap,
                pixel_shader=palette,
                x=item["icon_x"],
                y=WEEKLY_WEATHER_ICON_Y,
            ))
            self._temperature_label(
                group, item["max_text"], text_color, item["max_x"], WEEKLY_WEATHER_TEMPERATURE_Y
            )

    def _today_weather(self, group, screen):
        import displayio

        layout = _today_weather_layout(screen.get("blocks") or [])
        if not layout:
            text = "Weather unavailable"
            x = max(0, (DISPLAY_WIDTH - len(text) * WEATHER_FONT_WIDTH) // 2)
            self._label(group, text, 0xAAAAAA, x, 18)
            return
        stale = bool(screen.get("stale"))
        text_color = 0xAAAAAA if stale else 0xFFFFFF
        label_color = 0x777777 if stale else 0xFFAA00
        for item in layout:
            self._label(group, item["label"], label_color, item["label_x"], WEATHER_HEADING_BASELINE_Y)
            bitmap = displayio.Bitmap(item["icon_width"], item["icon_width"], 2)
            palette = displayio.Palette(2)
            palette[0] = 0x000000
            palette.make_transparent(0)
            palette[1] = _weather_rgb(item["icon_name"], stale)
            for y, row in enumerate(item["icon_rows"]):
                for x, pixel in enumerate(row):
                    if pixel == "#":
                        for dx in range(TODAY_WEATHER_ICON_SCALE):
                            for dy in range(TODAY_WEATHER_ICON_SCALE):
                                bitmap[x * TODAY_WEATHER_ICON_SCALE + dx,
                                       y * TODAY_WEATHER_ICON_SCALE + dy] = 1
            group.append(displayio.TileGrid(
                bitmap, pixel_shader=palette, x=item["icon_x"], y=TODAY_WEATHER_ICON_Y
            ))
            self._temperature_label(
                group, item["temp_text"], text_color, item["temp_x"], TODAY_WEATHER_TEMPERATURE_Y
            )

    def _sun_weather(self, group, screen, phase):
        import displayio

        stale = bool(screen.get("stale"))
        text_color = 0xAAAAAA if stale else 0xFFFFFF
        label_color = 0x777777 if stale else 0xFFAA00
        values = (
            ("SUNRISE", _format_sun_time(screen.get("sunrise_time")), "clear_day", 0, DISPLAY_WIDTH // 2),
            ("SUNSET", _format_sun_time(screen.get("sunset_time")), "clear_night", DISPLAY_WIDTH // 2, DISPLAY_WIDTH),
        )
        icon_grids = []
        label_grids = []
        for label, value, icon_name, left, right in values:
            width = right - left
            if icon_name == "clear_day":
                for index, character in enumerate(label):
                    label_grid, label_palette = self._sun_text_label(
                        group, character, _sun_weather_rise_label_color(index, phase, stale),
                        left + 27 + index * 8, 11, SUN_WEATHER_TIME_SCALE,
                    )
                    label_grids.append(("rise", index, label_grid, label_palette))
            else:
                for index, character in enumerate(label):
                    label_grid, label_palette = self._sun_text_label(
                        group, character, _sun_weather_set_label_color(index, phase, stale),
                        left + 27 + index * 8, 11, SUN_WEATHER_TIME_SCALE,
                    )
                    label_grids.append(("set", index, label_grid, label_palette))
            rows = WEATHER_ICONS[icon_name]
            icon_scale = (
                SUN_WEATHER_ICON_SCALE
                if icon_name == "clear_day"
                else SUN_WEATHER_MOON_ICON_SCALE
            )
            icon_width = WEATHER_ICON_WIDTH * icon_scale
            bitmap = displayio.Bitmap(icon_width, icon_width, 2)
            palette = displayio.Palette(2)
            palette[0] = 0x000000
            palette.make_transparent(0)
            palette[1] = _sun_weather_rgb(icon_name, stale, phase)
            for y, row in enumerate(rows):
                for x, pixel in enumerate(row):
                    if pixel == "#":
                        for dx in range(icon_scale):
                            for dy in range(icon_scale):
                                bitmap[x * icon_scale + dx, y * icon_scale + dy] = 1
            icon_grid = displayio.TileGrid(
                bitmap,
                pixel_shader=palette,
                x=left + 1 + (WEATHER_ICON_WIDTH * SUN_WEATHER_ICON_SCALE - icon_width) // 2,
                y=_sun_weather_icon_y(icon_name, phase),
            )
            group.append(icon_grid)
            icon_grids.append((icon_name, icon_grid))
            self._sun_text_label(group, value, text_color, left + 88, 11, SUN_WEATHER_TIME_SCALE)
        return tuple(icon_grids), tuple(label_grids)

    def _sun_text_label(self, group, text, color, x, y, scale):
        import displayio

        text = str(text)
        bitmap = displayio.Bitmap(len(text) * 4 * scale, 5 * scale, 2)
        palette = displayio.Palette(2)
        palette[0] = 0x000000
        palette.make_transparent(0)
        palette[1] = color
        for index, char in enumerate(text):
            rows = WEEKLY_WEATHER_GLYPHS.get(char, (0, 0, 0, 0, 0))
            for row_index, row_bits in enumerate(rows):
                for column in range(WEEKLY_WEATHER_GLYPH_WIDTH):
                    if row_bits & (1 << (WEEKLY_WEATHER_GLYPH_WIDTH - column - 1)):
                        for dx in range(scale):
                            for dy in range(scale):
                                bitmap[index * 4 * scale + column * scale + dx,
                                       row_index * scale + dy] = 1
        grid = displayio.TileGrid(bitmap, pixel_shader=palette, x=x, y=y)
        group.append(grid)
        return grid, palette

    def _show_sun_weather(self, screen, phase):
        import displayio

        key = (
            screen.get("sunrise_time") or "--:--",
            screen.get("sunset_time") or "--:--",
            bool(screen.get("stale")),
        )
        if (
            self._sun_group is None
            or self._sun_key != key
            or self.display.root_group is not self._sun_group
        ):
            group = displayio.Group()
            self._sun_icon_grids, self._sun_label_grids = self._sun_weather(group, screen, phase)
            self._sun_group = group
            self._sun_key = key
            self._present(group)
            return

        changed = False
        stale = bool(screen.get("stale"))
        for icon_name, icon_grid in self._sun_icon_grids:
            next_y = _sun_weather_icon_y(icon_name, phase)
            next_color = _sun_weather_rgb(icon_name, stale, phase)
            if icon_grid.y != next_y or icon_grid.pixel_shader[1] != next_color:
                icon_grid.y = next_y
                icon_grid.pixel_shader[1] = next_color
                changed = True
        for label_kind, index, label_grid, palette in self._sun_label_grids:
            next_color = (
                _sun_weather_rise_label_color(index, phase, stale)
                if label_kind == "rise"
                else _sun_weather_set_label_color(index, phase, stale)
            )
            if palette[1] != next_color:
                palette[1] = next_color
                changed = True
        if changed:
            self._refresh(animation_class="weather_sun_slide")

    def _bin_collection_cache_matches(self, screen, clock_date, header_kind):
        items = screen.get("collections") or []
        key = (
            str(screen.get("title") or "NEXT COLLECTION"),
            " / ".join(str(item.get("label") or "") for item in items),
            _bin_collection_due_label(screen.get("collection_date"), clock_date),
            bool(screen.get("stale")),
            _bin_collection_types(screen),
        )
        weather = screen.get("weather")
        return (
            self._bin_group is not None
            and self._bin_key == key
            and self._bin_header_kind == header_kind
            and self._bin_weather == weather
        )

    def _build_bin_icon(self, group, name, x):
        import displayio

        bitmap = displayio.Bitmap(BIN_ICON_WIDTH, BIN_ICON_HEIGHT, 3)
        palette = displayio.Palette(3)
        palette[0] = 0x000000
        palette.make_transparent(0)
        palette[1] = BIN_COLORS[name]
        palette[2] = 0x111111

        def rect(left, top, width, height, value):
            for px in range(left, left + width):
                for py in range(top, top + height):
                    if 0 <= px < BIN_ICON_WIDTH and 0 <= py < BIN_ICON_HEIGHT:
                        bitmap[px, py] = value

        rect(3, 0, 3, 1, 1)  # handle
        rect(0, 1, BIN_ICON_WIDTH, 2, 1)  # lid
        rect(1, 3, BIN_ICON_WIDTH - 2, 7, 1)  # body
        rect(2, 10, 2, 2, 2)
        rect(5, 10, 2, 2, 2)
        grid = displayio.TileGrid(bitmap, pixel_shader=palette, x=x, y=BIN_ICON_Y)
        group.append(grid)

    def _build_bin_lorry(self):
        import displayio

        bitmap = displayio.Bitmap(BIN_LORRY_WIDTH, BIN_LORRY_HEIGHT, 5)
        palette = displayio.Palette(5)
        palette[0] = 0x000000
        palette.make_transparent(0)
        palette[1] = 0x22AA44  # recycling body
        palette[2] = 0xFFAA00  # cab
        palette[3] = 0xDDEEFF  # windows / highlights
        palette[4] = 0x222222  # wheels

        def rect(left, top, width, height, value):
            for px in range(left, left + width):
                for py in range(top, top + height):
                    if 0 <= px < BIN_LORRY_WIDTH and 0 <= py < BIN_LORRY_HEIGHT:
                        bitmap[px, py] = value

        rect(2, 5, 32, 10, 1)
        rect(0, 8, 4, 7, 1)
        rect(32, 7, 17, 8, 2)
        rect(36, 4, 11, 4, 2)
        rect(37, 6, 6, 3, 3)
        rect(44, 6, 4, 3, 3)
        rect(49, 12, 3, 3, 3)
        # Three tiny highlight marks suggest the recycling arrows without
        # making the lorry noisy at 1-pixel LED resolution.
        for px, py in ((17, 8), (18, 8), (19, 9), (18, 10),
                       (20, 10), (21, 9), (22, 8), (23, 8)):
            bitmap[px, py] = 3
        for center in (12, 40):
            rect(center - 1, 14, 3, 1, 4)
            rect(center - 2, 15, 5, 3, 4)
            rect(center - 1, 18, 3, 1, 4)
            rect(center - 1, 16, 2, 2, 3)
        grid = displayio.TileGrid(bitmap, pixel_shader=palette, x=DISPLAY_WIDTH, y=6)
        # The lorry travels left, so put the cab on the leading (left) side.
        grid.flip_x = True
        return grid

    def _build_bin_collection(self, screen, clock_time, clock_date, phase, header_kind):
        import displayio

        group = displayio.Group()
        content = displayio.Group()
        title = str(screen.get("title") or "NEXT COLLECTION")
        items = screen.get("collections") or []
        labels = " / ".join(str(item.get("label") or "") for item in items)
        self._bin_title = self._label(content, _clip(title, 40), 0xFFAA00, 0, 3)
        self._bin_types = _bin_collection_types(screen)
        bin_width = len(self._bin_types) * (BIN_ICON_WIDTH + 2) - 2
        due_label = _bin_collection_due_label(screen.get("collection_date"), clock_date)
        due_width = len(due_label) * WEATHER_FONT_WIDTH
        type_width = max(
            0,
            DISPLAY_WIDTH - BIN_LORRY_WIDTH - due_width - bin_width - HEADER_GAP * 3,
        )
        type_label = _fit_text_pixels(labels, type_width)
        type_label_width = len(type_label) * WEATHER_FONT_WIDTH
        group.append(content)
        self._bin_content_group = content
        self._bin_lorry_group = displayio.Group()
        self._bin_lorry_grid = self._build_bin_lorry()
        self._bin_lorry_grid.x = 0
        self._bin_lorry_group.append(self._bin_lorry_grid)
        self._bin_lorry_label = self._label(
            self._bin_lorry_group,
            type_label,
            0xFFFFFF,
            BIN_LORRY_WIDTH + HEADER_GAP,
            14,
        )
        due_x = BIN_LORRY_WIDTH + HEADER_GAP * 2 + type_label_width
        self._bin_date = self._label(self._bin_lorry_group, due_label, 0xAAAAAA, due_x, 14)
        self._bin_bins_group = displayio.Group()
        self._bin_bins_group.x = due_x + due_width + HEADER_GAP
        for index, name in enumerate(self._bin_types):
            self._build_bin_icon(self._bin_bins_group, name, index * (BIN_ICON_WIDTH + 2))
        self._bin_lorry_group.append(self._bin_bins_group)
        group.append(self._bin_lorry_group)
        self._bin_footer_group = self._bin_lorry_group
        self._bin_date_group = self._bin_lorry_group
        self._bin_label = self._bin_lorry_label
        if screen.get("stale"):
            self._bin_stale = self._label(group, "STALE", 0xFF3300, STALE_X, 3)
        else:
            self._bin_stale = None
        self._mask(group, HEADER_SLOT_X, 0, HEADER_SLOT_WIDTH, 8)
        if header_kind == "weather":
            self._bin_header_group = displayio.Group()
            self._header_weather(self._bin_header_group, screen.get("weather"), 0)
            group.append(self._bin_header_group)
            self._bin_clock_label = None
        else:
            self._bin_header_group = None
            self._bin_clock_label = self._label(group, clock_time, 0xFFAA00, CLOCK_X, 3)
        self._bin_group = group
        self._bin_header_kind = header_kind
        self._bin_weather = dict(screen["weather"]) if isinstance(screen.get("weather"), dict) else None
        self._bin_key = (
            title,
            labels,
            _bin_collection_due_label(screen.get("collection_date"), clock_date),
            bool(screen.get("stale")),
            self._bin_types,
        )

    def _show_bin_collection(self, screen, clock_time, clock_date, phase):
        update_started = time.monotonic()
        header_kind, header_offset = _header_item_state(phase, screen.get("weather"))
        if not self._bin_collection_cache_matches(screen, clock_date, header_kind):
            self._build_bin_collection(screen, clock_time, clock_date, phase, header_kind)
            changed = True
        else:
            changed = False
        try:
            elapsed = max(0.0, float(phase or 0))
        except (TypeError, ValueError):
            elapsed = 0.0
        next_lorry_x = _bin_lorry_x(min(elapsed, BIN_LORRY_SECONDS))
        if self._bin_lorry_group.x != next_lorry_x:
            self._bin_lorry_group.x = next_lorry_x
            changed = True
        if self._bin_clock_label is not None:
            if self._bin_clock_label.text != clock_time:
                self._bin_clock_label.text = clock_time
                changed = True
            next_x = CLOCK_X + header_offset
            if self._bin_clock_label.x != next_x:
                self._bin_clock_label.x = next_x
                changed = True
        elif self._bin_header_group is not None and self._bin_header_group.x != header_offset:
            self._bin_header_group.x = header_offset
            changed = True
        self._attach_brightness_overlay(self._bin_group)
        if self.display.root_group is not self._bin_group:
            self.display.root_group = self._bin_group
            changed = True
        if changed:
            animation_class = self._animation_class(screen, phase)
            self._refresh(animation_class=animation_class)
        else:
            animation_class = self._animation_class(screen, phase)
        self._record_animation_update(
            "bin_collection", changed, time.monotonic() - update_started, animation_class
        )

    def _header_weather(self, group, weather, offset=0):
        if not isinstance(weather, dict):
            return
        import displayio

        text, icon_x, text_x = _weather_group_layout(weather, offset)
        icon_name, rows = _weather_icon(weather)
        stale = bool(weather.get("stale"))
        bitmap = displayio.Bitmap(WEATHER_ICON_WIDTH, 8, 2)
        palette = displayio.Palette(2)
        palette[0] = 0x000000
        palette[1] = _weather_rgb(icon_name, stale)
        for y, row in enumerate(rows):
            for x, pixel in enumerate(row):
                if pixel == "#":
                    bitmap[x, y] = 1
        group.append(displayio.TileGrid(bitmap, pixel_shader=palette, x=icon_x, y=0))
        self._label(group, text, 0xAAAAAA if stale else 0xFFFFFF, text_x, 3)

    def show(self, screen, clock_time="--:--", clock_date="", phase=2):
        import displayio

        empty_state = screen.get("empty_state")
        kind = screen.get("kind")
        if not empty_state and kind in ("dad_joke", "random_fact"):
            group = displayio.Group()
            heading = "DAD JOKE" if kind == "dad_joke" else "DID YOU KNOW?"
            self._label(group, heading, 0xFFAA00, 0, NOVELTY_HEADING_Y)
            for index, line in enumerate(_novelty_page(screen, phase)):
                self._label(group, line, 0xFFFFFF, 0, NOVELTY_FIRST_LINE_Y + index * 8)
            self._present(group)
            return
        if not empty_state and kind == "flash":
            self._show_flash(screen, phase)
            return

        if not empty_state and kind == "steam_train_intro":
            self._show_steam_train(screen, phase)
            return

        if not empty_state and kind == "bin_collection":
            self._show_bin_collection(screen, clock_time, clock_date, phase)
            return

        if (
            not empty_state
            and kind == "calendar_agenda"
            and screen.get("source") == "todoist"
        ):
            self._show_todoist(screen, clock_time, clock_date, phase)
            return

        if not empty_state and kind == "rail_combined":
            self._show_rail(screen, clock_time, phase)
            return

        if not empty_state and kind in WEATHER_FULLSCREEN_KINDS:
            if kind == "weather_sun":
                self._show_sun_weather(screen, phase)
                return
            group = displayio.Group()
            if kind == "weather_weekly":
                self._weekly_weather(group, screen)
            else:
                self._today_weather(group, screen)
            self._present(group)
            return

        group = displayio.Group()
        if empty_state:
            text = _clip(empty_state, 30)
            x = max(0, (DISPLAY_WIDTH - len(text) * WEATHER_FONT_WIDTH) // 2)
            self._label(group, text, 0xFFFFFF, x, 18)
            self._present(group)
            return
        if kind == "rail_combined":
            self._rail(group, screen, phase)
        elif kind == "theme_park_queues":
            self._queues(group, screen, phase)
        elif kind == "calendar_agenda":
            self._calendar(group, screen, phase, clock_date)
        elif kind == "flash":
            self._flash(group, screen, phase)
        else:
            self._label(group, _clip(screen.get("title") or "Display unavailable", 30), 0xFFFFFF, 0, 3)
        due_text, due_x = _calendar_due_layout(screen, clock_date, clock_time)
        if due_text:
            self._label(group, due_text, 0xFFFFFF, due_x, 3)
        if screen.get("stale"):
            self._label(group, "STALE", 0xFF3300, STALE_X, 3)
        self._mask(group, HEADER_SLOT_X, 0, HEADER_SLOT_WIDTH, 8)
        item, offset = _header_item_state(phase, screen.get("weather"))
        if item == "weather":
            self._header_weather(group, screen.get("weather"), offset)
        else:
            self._label(group, clock_time, 0xFFAA00, CLOCK_X + offset, 3)
        self._present(group)
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
