antonio1000homens/led/hardware/matrixportal/firmware/mqtt_client.py

"""Optional CircuitPython MQTT transport for reminder and cycle screens.

This module is intentionally not imported unless both local opt-in flags are
enabled. It contains no credentials or broker defaults.
"""

MQTT_LOOP_INTERVAL_SECONDS = 60.0
MQTT_KEEP_ALIVE_SECONDS = 180
MQTT_SOCKET_TIMEOUT_SECONDS = 0.01


class FlashMqttClient:
    def __init__(
        self,
        settings,
        on_message,
        mqtt_factory=None,
        startup_delay_seconds=0.0,
        started_at=None,
    ):
        self.settings = settings
        self.on_message = on_message
        self.mqtt_factory = mqtt_factory
        startup_delay_seconds = float(startup_delay_seconds)
        if startup_delay_seconds < 0:
            raise ValueError("startup_delay_seconds must be non-negative")
        self.connect_after = 0.0
        if startup_delay_seconds:
            if started_at is None:
                import time

                started_at = time.monotonic()
            self.connect_after = float(started_at) + startup_delay_seconds
        self.client = None
        self.connected = False
        self.enabled = True
        self.next_attempt = 0
        self.next_loop = 0

    def set_enabled(self, enabled):
        """Apply the admin runtime gate and close the connection when disabled."""
        enabled = bool(enabled)
        if self.enabled == enabled:
            return
        self.enabled = enabled
        if not enabled:
            self._discard_client()
            self.next_attempt = 0

    def _connect(self, now):
        if self.client is not None and self.connected:
            return
        if now < self.next_attempt:
            return
        if not self.settings.MQTT_BROKER:
            return
        try:
            if self.mqtt_factory is None:
                import adafruit_connection_manager
                import adafruit_minimqtt.adafruit_minimqtt as MQTT
                import wifi

                if not wifi.radio.connected:
                    wifi.radio.connect(self.settings.WIFI_SSID, self.settings.WIFI_PASSWORD)
                pool = adafruit_connection_manager.get_radio_socketpool(wifi.radio)
                self.client = MQTT.MQTT(
                    broker=self.settings.MQTT_BROKER,
                    port=self.settings.MQTT_PORT,
                    username=self.settings.MQTT_USERNAME or None,
                    password=self.settings.MQTT_PASSWORD or None,
                    socket_pool=pool,
                    keep_alive=MQTT_KEEP_ALIVE_SECONDS,
                    socket_timeout=MQTT_SOCKET_TIMEOUT_SECONDS,
                )
            else:
                self.client = self.mqtt_factory(self.settings)
            self.client.on_message = lambda client, topic, message: self.on_message(topic, message)
            self.client.connect()
            self.client.subscribe(self.settings.MQTT_TOPIC, qos=1)
            screen_topic = getattr(self.settings, "MQTT_SCREENS_TOPIC", "led/screens/+")
            self.client.subscribe(screen_topic, qos=1)
            self.connected = True
            self.next_loop = now
            print("MQTT subscribed reminder={} screens={}".format(self.settings.MQTT_TOPIC, screen_topic))
        except Exception as error:
            self._discard_client()
            self.next_attempt = now + 30
            print("MQTT unavailable:", error)

    def _discard_client(self):
        client = self.client
        self.connected = False
        self.client = None
        self.next_loop = 0
        if client is not None:
            try:
                disconnect = getattr(client, "disconnect", None)
                if disconnect is not None:
                    disconnect()
            except Exception:
                pass

    def poll(self, now, allow_connect=True):
        if not self.enabled:
            return
        # A Wi-Fi/MQTT handshake can block far longer than socket_timeout.
        # Avoid starting one in the middle of a visible animation.
        if not self.client or not self.connected:
            if not allow_connect or now < self.connect_after:
                return
            self._connect(now)
        if not self.client or not self.connected:
            return
        if now < self.next_loop:
            return
        try:
            # Keep MiniMQTT's blocking read below one 8 FPS display frame.
            # Receive retained screen/reminder snapshots once a minute; due-time checks use no I/O.
            # Keepalive spans three polls so the broker tolerates this cadence.
            self.client.loop(timeout=MQTT_SOCKET_TIMEOUT_SECONDS)
            self.next_loop = now + MQTT_LOOP_INTERVAL_SECONDS
        except Exception as error:
            self._discard_client()
            self.next_attempt = now + 5
            print("MQTT disconnected:", error)
