antonio1000homens/led/hardware/matrixportal/firmware/matrix_runtime.py

"""Pure runtime mode state for the MatrixPortal application."""


DIAGNOSTIC_COLORS = (
    ("RED", 0x400000),
    ("GREEN", 0x004000),
    ("BLUE", 0x000040),
    ("WHITE", 0x202020),
    ("BLACK", 0x000000),
)


class RuntimeMode:
    """Track normal/diagnostic mode without depending on CircuitPython APIs."""

    def __init__(self):
        self.mode = "normal"
        self.diagnostic_index = 0

    def handle(self, event, rotation=None, now=None):
        """Handle one debounced button event.

        Return ``True`` when the displayed mode/diagnostic colour changed.
        Long UP toggles diagnostics; long DOWN advances the normal rotation.
        """
        if event == "up_long":
            self.mode = "diagnostic" if self.mode == "normal" else "normal"
            return True
        if event == "down" and self.mode == "diagnostic":
            self.diagnostic_index = (self.diagnostic_index + 1) % len(DIAGNOSTIC_COLORS)
            return True
        if event == "down_long" and self.mode == "normal" and rotation is not None:
            rotation.next(now)
        return False

    def diagnostic(self):
        return DIAGNOSTIC_COLORS[self.diagnostic_index]
